SuperTapir/CadenzaOS/assets/typography/review/2026-07-19/typography-matrix-index.md

# Typography visual matrix

Columns: T-Embed 320×170, Sharp 400×240.

1. `launcher`
2. `timer-ready`
3. `timer-running`
4. `timer-paused`
5. `timer-alert`
6. `timer-starting-mid`
7. `timer-pausing-mid`
8. `timer-resuming-mid`
9. `timer-alert-mid`
10. `motion`
11. `settings`
12. `gallery-easing`
13. `gallery-selection`
14. `gallery-sprite`
15. `system-menu`
16. `system-overlay`
17. `role-long-inverse`

Contact sheet: `typography-contact-sheet.png`
