SuperTapir/CadenzaOS/assets/launcher-covers/review/2026-07-19-non-timer-refresh/gallery/review.md

# ANIMATION GALLERY v1 visual review

- Exact title: pass (`ANIMATION GALLERY`, complete and immediately legible in both profiles).
- Bold layout: pass; the title forms full-width top and bottom stage walls rather than a left-title/right-object template.
- Functional hook: pass; one repeated figure appears in exactly three successive poses along one easing arc.
- Element budget: pass; no frame numbers, axes, secondary curves, particles, camera marks or unrelated icons.
- Hard-threshold recognition: pass at 350×155 and 280×124; title, three poses and single trajectory remain recognizable without gray.
- Tonal discipline: pass; one concentrated halftone field supports the stage depth without entering title counters.
- Contour cleanup: pass with five bands plus `--edge-cleanup`; nearest-neighbor 4× inspection shows regular title and figure contours without patterned halos.
- Visual approval: explicitly approved by the user in this task on 2026-07-19 (`ok`).
- Formal source SHA-256: `856bd02c42c6160959b00fe79b05e403dc9a1034ae98b91581be47714985e979`.
