SuperTapir/CadenzaOS/docs/app-handoff-reference-research.md

# App Handoff 与 System Menu 动效参考调研

日期：2026-07-19
适用 change：`align-app-cover-handoff`

## 结论

- Launcher 只拥有从轨道/card chrome 到 App 身份的系统交接；App 入场后半段不是统一模板，而是每款 App 独立的 launch sequence。
- 静态 Cover 与 launch sequence 必须分开：Cover 继续是不可变的目录身份，launch renderer 是可 seek、无 lifecycle side effect 的全屏纯绘制能力。
- 返回 Launcher 不倒放各 App 的入场动画，而使用当前 App 的静态 Cover bridge，形成更快的“收回卡片”语义。
- System Menu 是独立 system surface：右侧面板快速滑入、完整滑出；关闭期间底层 App 继续冻结且输入仍属于 Menu。

## 四段视频逐帧证据

| 文件 | 尺寸 / 时长 | 关键时间点 | 结论 |
|---|---:|---|---|
| `PixPin_2026-07-19_00-34-52.mp4` | 460×452 / 5.75 s | 约 2.85 s 启动；3.00 s chrome 退场；3.15–3.20 s dither 到黑；3.65 s App 首屏 | 系统先完成 Card/Launcher 交接，再揭示 App |
| `PixPin_2026-07-19_00-46-18.mp4` | 660×654 / 5.625 s | 约 1.25 s pressed 反馈；1.75–1.95 s chrome 退场；2.05–3.65 s `MUSIC BOX` 专属标题/扫描线；3.75 s 曲目 UI | launch sequence 属于 Music Box 自身，不是统一系统缩放 |
| `PixPin_2026-07-19_00-47-57.mp4` | 622×376 / 5.792 s | 约 1.85 s Launcher chrome 消失；人物画面继续占满屏幕并持续变化 | 另一 App 使用完全不同的内容连续入场 |
| `PixPin_2026-07-19_00-50-54.mp4` | 946×506 / 4.5 s / 24 FPS | 1.208 s 尚未出现，1.250–1.417 s 为 5 个打开关键帧；3.833 s 稳定，3.875–4.042 s 为关闭形变，4.083 s 已离屏 | 打开顶部首帧到位、底部以近似 `out-cubic` 追上；关闭仍由顶部先离开而非倒放；底层 App 全程冻结可见 |

最初抽帧使用本机 FFmpeg 7.1，以 10 FPS contact sheet 和转场区间 20 FPS 复核。2026-07-19 的菜单二次校准改用 AVFoundation 按源视频 24 FPS 逐帧提取：打开前缘从左上到右下，第一可见帧顶部已在最终分界而底部仍接近屏幕右缘；随后底部可见比例约按 `0 → 0.5 → 0.87 → 1` 收束。关闭前缘方向反转为右上到左下，证明它不是打开帧的简单倒序。这些时间点用于确定阶段、曲线和数量级，不作为未经真机批准的永久像素 golden。

## 锁定上游契约

本机 Playdate SDK 固定为 1.12.3。`Inside Playdate.html` 明确规定：

- `card.png` 为 350×155；
- Launcher 在启动动画前把 card 放在 400×240 的 `(25, 43, 350, 155)`；
- `launchImages/1.png, 2.png, ...` 是每个 game 自己提供的 400×240 全屏 transition frames；
- `launchImage.png` 是 loading/末帧 fallback。

`Examples/Level 1-1/Source/SystemAssets` 的 `card.png`/`card-pressed.png` 均为 350×155，`launchImages/1..9.png` 均为 400×240；关键源码和资产尺寸已直接检查，没有只依赖 README。Cadenza 只采用“静态 Card -> 每 App 全屏序列 -> 首屏”的职责划分，不复制 SDK 示例像素、声音或品牌。

## 既有开源证据复用

本 change 复用 `docs/reference-research.md` 已锁定的源码级调研：

- NobleEngine `93ffd6eb29d61c1af1cb8d40b78daf75c4e85946`：采用 Cover transition 的中点 lifecycle 交接思想；不采用 Lua scene engine、logo 或 transition assets。
- Taxman Engine `51981885dcb9bb7b467cb578785ac68a084fd8ab`：采用 off-screen/dither 对场景合成有价值的结论；不采用 `calloc/realloc` render textures 与完整 ECS。
- LVGL `a73e59f6d144785012e44ab93f1f3d4dde48a180` / Tweeny `d50d96dfa61b115fb0d9fce59f7bbe4488f9b9b0`：采用可 seek/确定性时间语义；不采用动态 descriptor/callback 容器。

## 采用 / 不采用

采用：App 独立 const launch renderer、归一化 progress、系统中点 lifecycle、两张固定 framebuffer、ordered dither、Menu 显式 closing 状态、双 profile 快照与真机 P8。

不采用：给静态 Cover 增加 launching 状态、运行时缩放已二值化 Cover、第三张全屏 transition buffer、提前 `onEnter`、外部 PNG/PDI 文件协议、倒放 App launch sequence 作为返回、Menu close 瞬切。

## 2026-07-19 实现与验证记录

实现采用两阶段 handoff：默认 Launcher → App 为 0.80 秒，App → Launcher 为 0.44 秒；Reduced Motion 分别为 0.56 秒和 0.28 秒。Timer、Motion、Settings、Animation Gallery 均提供独立的代码原生全屏 launch renderer；未实现该能力的 App 使用居中的静态 Cover/受约束名称卡。System Menu 在右边缘锚定，逐 scanline 形成斜向前缘，并把完整面板横向重采样进当前可见宽度；Resume 关闭期间仍冻结 App、消费输入，Home 则直接交给 return handoff，避免叠加两条系统动画。

首轮视觉审阅指出 Cover、独立概念动画与真实 App UI 仍是三段不连续构图。连续版因此取消中间海报：progress 0 逐像素等于居中 Cover，progress 1 逐像素等于同一 App 状态和 SystemSnapshot 在 `onEnter` 后的真实首屏，中间以固定相位 ordered-dither 单调交接像素。Settings launch renderer 接收只读 AppRenderContext，避免 Motion/Sound/Connectivity 非默认状态在中点跳变；Timer、Motion、Settings 抽取与普通 render 共用的首屏 helper，Gallery 使用与 page 0/Easing 完全一致的初始帧 helper。

菜单二次校准把 Normal 开关时长从 0.16 秒调整为 0.20 秒。打开不再让整个面板统一 `out-quad` 平移，也不再使用只有 28% 的浅逐行 stagger；顶部 scanline 在第一可见帧直接锚定最终左边界，底部先等待 22% 行程再按 `out-cubic` 追上，各行线性插值形成强斜边并继续横向重采样内容。关闭单独建模：顶部立即向右离开，底部延迟 40% 行程后跟随。真实 HeadlessHost 以 24 FPS 捕获后，打开底部轨迹约为 `0 → 0.58 → 0.89 → 0.99 → 1`，与参考逐帧估计的 `0 → 0.5 → 0.87 → 0.99 → 1` 接近；关闭斜边方向、约 5 帧形变和 0.20 秒端点同样一致。这样保留端点与两 framebuffer/零分配约束，同时复现参考中的拉伸与回收方向；Reduced Motion 仍为 0.10 秒。

返回动画的完整 30 FPS 审阅又发现：原 `inOutQuad` 把 App → Cover 的 dither 变化集中到中间两帧，T-Embed 的旧 Clock/Gallery 峰值为 20.96%/21.50%，Sharp 最坏达到 22.90%；同时 Sharp 的 bridge 使用整数向下居中落在 `y=42`，与 Launcher 和 Playdate card 契约的 `(25,43,350,155)` 相差 1 px。修订后前半段改为匀速 threshold 交接，奇数剩余空间统一用向上取整的视觉中心；中点后 Cover 内容矩形逐像素保持不动，只让边框、scanline 与相邻卡片恢复。新版 T-Embed 四 App 峰值依次为 11.70%、7.07%、8.02%、12.23%，Sharp 为 12.17%、7.92%、8.49%、13.05%，均低于 16% 回归上限。

自动化验证结果：

- `cmake --build build -j4`：通过；
- `ctest --test-dir build --output-on-failure`：71/71 通过；
- 独立 `-Wall -Wextra -Wpedantic -Werror` 构建与 handoff/allocation/apps/snapshot/desktop focused suite：通过；
- 双 profile golden：四个内置 App 入场、无专属 renderer fallback、旧 Clock 返回、Menu opening/closing 均已生成 PNG 目检并锁定 hash；四 App 另以固定 30 FPS 生成完整进入与返回 PNG/GIF 时间轴；该记录描述迁名前的历史资产。
- endpoint regression 证明四 App `p0 == Cover`、`p1 == first App frame`；30 FPS 相邻帧变化不超过 framebuffer 像素的 20%；
- return regression 证明四 App 在双 profile 下 `p0 == outgoing App frame`，生命周期中点后的 Cover 矩形与 Launcher 逐像素一致且固定，`p1` 后下一帧不跳变；30 FPS 相邻变化不超过 16%；
- 完整进入 → Menu 开合 → 返回路径的 `operator new/new[]` 计数保持不变；host `AppRuntime` 为 24,928 B，其中两张固定 framebuffer 为 24,048 B，没有第三张全屏 buffer；
- PlatformIO T-Embed compile：RAM 99,248 / 327,680 B（30.3%），Flash 412,449 / 3,145,728 B（13.1%）。相对 WIP 前的 `HEAD` 基线增加 64 B RAM、3,452 B Flash；连续进入/返回版相对首轮海报式 WIP 减少 1,048 B Flash；
- Sharp launch renderer 的一次性 host 微基准平均约 1.74 ms/帧；它只用于发现明显退化，不替代 ESP32 真机 frame-time；
- 两 profile SDL dummy 各运行 180 帧、desktop input smoke、共享源码审计、OpenSpec strict 与 `git diff --check` 均通过。

自动化只批准像素确定性和系统语义。T-Embed 真机仍需以 30 FPS 检查 Memory LCD 的 dither 闪烁、拖影、0.80 秒入场是否拖沓、0.44 秒返回是否干脆，以及菜单 0.16 秒形变是否与参考视频一致；这些是 P8 人工视觉批准边界，host PNG 不能代替。
