SuperTapir/CadenzaOS/assets/launcher-covers/review/2026-07-19-about/about/prompt.md

# Cadenza OS About Logo v1 prompt record

## Identity brief

Cadenza OS 是承载个人小游戏、工具、动画与互动实验的创作平台；一枚开放的巨型 C 环同时暗示旋钮、唱片槽与留给创作者自由发挥的华彩空间，精确字标 `CADENZA OS` 从开口穿出，在黑白主质量与两块结构灰面中形成冷静、鲜明的系统身份。

## Visual strategy

`retro software package`，不使用 App Cover 的截图或设置面板语言。

## Permitted elements

1. 精确字标 `CADENZA OS`；
2. 一个开放式粗 C 环；
3. 一条与字标锁合的宽基线；
4. 最多一个节拍 / 旋钮定位缺口。

## Tonal plan

- 主黑质量：C 环外轮廓、字标主面与基线；
- 主白质量：安静背景、开放 C 内部和字母 counter；
- 中灰面：C 环侧壁，表达厚度；
- 浅灰面：字标或基线的单一侧面，表达遮挡顺序。

## Generation prompt

Use case: logo-brand
Asset type: Cadenza OS About-screen identity lockup, prepared as a 350:155 micro-poster master
Primary request: Design an original Cadenza OS identity lockup whose recall hook is one enormous open C-shaped ring. The ring simultaneously suggests a rotary control, a record groove, and an open space for personal improvisation. The exact wordmark `CADENZA OS` emerges through the opening and locks into one broad baseline. The wordmark stays flat, frontal, complete, and instantly readable; the ring may sit behind and partly around it with an unambiguous occlusion order. Use only the exact wordmark, the open C ring, the broad baseline, and at most one bold index notch. Do not invent an icon family or extra symbols.
Input images: the four existing CadenzaOS Launcher Cover masters are style references only; do not copy their individual layouts or objects.
Scene/backdrop: one broad quiet field, balanced black and white masses, no external frame.
Style/medium: original restrained industrial monochrome software-package mark, bold editorial geometry, smooth high-resolution illustration designed for later ordered-dither conversion.
Composition/framing: strict landscape 350:155 ratio, safe crop for 1400x620, wordmark carries roughly half the visual weight, complete title inside generous safe margins.
Color palette: pure black, white, one middle gray side wall, one light gray overlap plane only.
Text (verbatim): `CADENZA OS` — spell C-A-D-E-N-Z-A, space, O-S, exactly once; no other text.
Constraints: hard pure-black-and-white threshold must preserve the wordmark, open C silhouette, and their overlap; critical contours broad and continuous; three to five discrete hard-boundary planes; smooth antialiased master edges; distinctive but compatible with the existing CadenzaOS TIMER, MOTION, SETTINGS, and ANIMATION GALLERY micro-posters.
Avoid: imitation of a specific Playdate cover or logo, copied lettering, musical notes, treble clefs, waveforms, keyboards, gears, circuit boards, settings controls, dashboards, buttons, screws, bolts, tiny labels, decorative ticks, multiple rings, external card frame, rounded container, generic mobile UI, photorealism, studio lighting, continuous gradients, soft shadows, contact shadows, ambient occlusion, glossy bevels, specular highlights, blur, random texture, pre-pixelated jagged edges, extra words, misspelling.

Shared medium direction: original restrained industrial 1-bit micro-poster identity art for a reflective monochrome handheld, exact title integrated as a large immediately legible primary graphic occupying roughly one third to one half of the composition, one instantly memorable relationship, bold black and white massing that preserves both title and hook under a hard pure-black-and-white threshold before any texture, large legible silhouettes, purposeful editorial composition, radical visual economy, coherent cool industrial house style, high-resolution smooth master designed for later 1-bit ordered-dither conversion, deliberate gray values used only as broad planar surfaces that clarify front face, side face and overlap, dimensional through scale and overlap rather than decorative clutter, no card border, landscape 350:155 aspect ratio, title fully inside safe margins.

## v1 review — rejected

The generated v1 is rejected before conversion. Although the title is exact and
the silhouette is strong, the oversized C reads as a generic mechanical dial or
hardware-company emblem. It does not communicate Cadenza's defining idea: a
stable system that deliberately leaves room for personal improvisation. The
mark also has no space for the requested elegant slogan. It must not become a
formal asset.

## v2 identity brief

一个克制、稳定的 `CADENZA` 主字标代表统一系统结构，紧凑的 `OS` 铭牌扣在末端；唯一一条自由笔势从严格基线中逸出、穿过字标并舒展开来，表达“规则中的即兴”，花体 slogan `A Space to Improvise.` 沿这条笔势落下。

## v2 permitted elements

1. 精确主字标 `CADENZA`；
2. 精确小型铭牌 `OS`；
3. 一条从规整基线逸出的连续自由笔势；
4. 精确 slogan `A Space to Improvise.`。

## v2 tonal plan

- 主白质量：宽阔、安静的背景与字母 counter；
- 主黑质量：`CADENZA` 字标和严格基线；
- 中灰面：自由笔势经过字标背后的单一遮挡段；
- 浅灰面：`OS` 铭牌的单一侧面。

## v2 concept review — rejected before generation

The free-stroke wordmark remains too abstract. It would explain the idea only
after reading a design rationale, rather than making Cadenza vivid at a glance.

## v3 identity brief

`CADENZA` 字标直接构成一座开放舞台 / 幕框，一位唯一的 solo performer 从规整结构中走进一束宽聚光平面自由发挥；紧凑的 `OS` 铭牌属于舞台结构，花体 slogan `A Space to Improvise.` 像签名落在下方。舞台是“为个人作品提供空间”，solo moment 是音乐术语 cadenza 的直接形象。

## v3 permitted elements

1. 精确主字标 `CADENZA`，同时充当舞台结构；
2. 精确小型铭牌 `OS`；
3. 一位大轮廓、无具体身份的 solo performer；
4. 一束宽聚光平面；
5. 精确 slogan `A Space to Improvise.`。

## v3 tonal plan

- 主白质量：舞台外的安静背景与开放空间；
- 主黑质量：字标舞台和人物轮廓；
- 中灰面：宽聚光平面，用于把人物从结构中分离；
- 浅灰面：舞台单一侧面，用于表达开口与深度。

## v3 concept review — superseded before generation

A generic performer and spotlight are pictorial, but the scene still needs a
specific musical object to make the name Cadenza immediate rather than merely
theatrical.

## v4 identity brief

一架高度简化的三角钢琴以打开的琴盖形成唯一大剪影，同时像向个人创作展开的舞台；精确字标 `CADENZA OS` 成为琴身侧面的结构，花体 slogan `A Space to Improvise.` 像演奏者签名沿下方落下。它以一个物件直接表达 cadenza 的独奏、优雅与自由发挥。

## v4 permitted elements

1. 精确主字标 `CADENZA OS`；
2. 一架高度简化的三角钢琴，仅保留琴身、打开的琴盖与一段宽键盘；
3. 精确花体 slogan `A Space to Improvise.`。

## v4 tonal plan

- 主白质量：安静背景、字标与琴键间隙；
- 主黑质量：钢琴连续外轮廓与字标支撑面；
- 中灰面：打开的琴盖内面，表达舞台式展开；
- 浅灰面：琴身唯一侧面，表达字标所在结构。
