SuperTapir/CadenzaOS/assets/launcher-covers/review/2026-07-19-non-timer-refresh/settings/review.md

# SETTINGS v1 visual review

- Exact title: pass (`SETTINGS`, once, complete and immediately legible in both profiles).
- Bold layout: pass; the title spans the center as the deck faceplate and does not reuse a left-title/right-object template.
- Functional hook: pass; rotary dial, toggle and slider form one tactile deck on a common base.
- Element budget: pass; no list, labels, Wi-Fi icon, screws, calibration ticks, extra panel or floating prop.
- Hard-threshold recognition: pass at 350×155 and 280×124; title and three control categories survive without gray.
- Hierarchy: pass; the bottom slider is intentionally subordinate but remains at least two pixels thick and readable as a horizontal control at 1×.
- Tonal discipline: pass; gray is limited to broad top/front/side deck planes.
- Contour cleanup: pass with five bands plus `--edge-cleanup`; nearest-neighbor 4× inspection shows clean title/control silhouettes without Bayer fringe touching critical edges.
- House distinction: pass; the central full-width deck differs from TIMER's overlap and MOTION's left-low kinetic wordmark.
- Grayscale-master style: fail after formal reflective review; continuous studio lighting, soft contact shadows, ambient occlusion and rounded product-render bevels make the 1-bit result read like a converted photograph rather than an illustration.
- Outer silhouette: fail after formal reflective review; the pale top plane and dithered side plane do not create a sufficiently continuous, independent deck contour.
- Visual approval: withdrawn after the user reviewed the formal reflective output on 2026-07-19. Preserve this candidate as rejected v1; do not use it as a formal baseline.
