SuperTapir/CadenzaOS/openspec/changes/archive/2026-07-18-add-bounded-text-layout/proposal.md

## Why

Cadenza 当前允许菜单调用方以固定倍数绘制动态文本，却不要求声明可用区域或溢出行为。因此，较长的应用名称和菜单信息会被截断、越过容器边界，或侵占相邻元素；虽然 framebuffer 的内存仍然安全，但最终菜单呈现已经失效。

## What Changes

- 增加确定性的受约束文本布局契约：绘制前，先根据调用方提供的矩形区域测量文本。
- 显式支持自适应缩放、省略号截断、换行和跑马灯等溢出策略；文本在最小倍数下仍无法容纳时，必须执行稳定且明确的降级行为。
- 将“内容约束”与“呈现方式”分离：裁剪只作为最终安全边界，布局阶段必须在光栅化之前选出完整且符合预期的呈现结果。
- 将 Launcher 主标题、左右相邻应用名及其他动态菜单标签从固定倍数绘制迁移到受约束布局。
- 为菜单中的主内容、次要标签、导航指示器和边框划分互不侵占的显式区域。
- 为两种受支持的 framebuffer profile、超长异常文本以及菜单元素互不重叠补充回归测试。

## Capabilities

### New Capabilities

- `bounded-text-layout`：规定动态文本在受限 UI 区域内进行确定性测量、自适应、降级和边界约束的行为，并规定菜单消费者如何为动态标签分配独立区域。

### Modified Capabilities

无。仓库目前没有已归档的主 spec；Launcher 的采用行为统一记录在新 capability 中。

## Impact

- 影响可移植的 `MonoCanvas` 文本 API，或建立在其上的小型 presentation 层辅助模块；同时影响 Launcher 的动态文本绘制与菜单区域划分。
- 不改变 framebuffer 尺寸、应用切换逻辑、输入语义或桌面调试 HUD 的现有覆盖式呈现。
- 增加可移植布局测试，以及 Launcher 在 320×170 和 400×240 下的快照、边界和元素重叠回归用例。
- 不引入新的运行时依赖，固件侧不新增预期 heap 分配；布局结果必须保持确定性，并适配固定容量约束。
