SuperTapir/CadenzaOS/assets/industrial-design/3d/cadenza-concept-v1-back.png

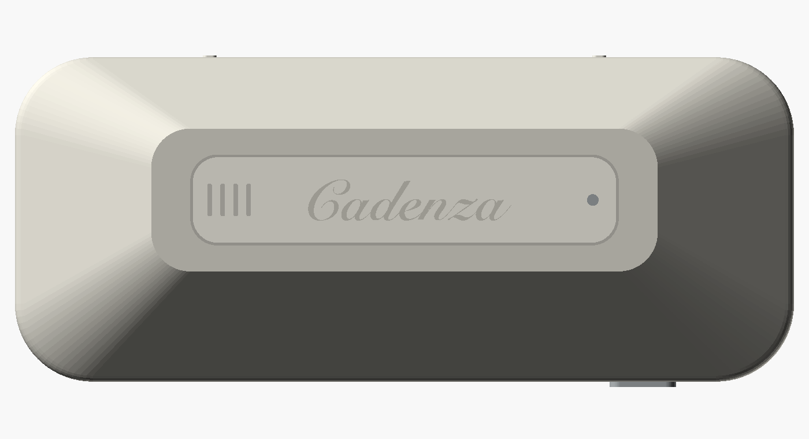
assets/industrial-design/3d/cadenza-concept-v1-back.png
