SuperTapir/CadenzaOS/assets/industrial-design/3d/cadenza-concept-v1-front.png

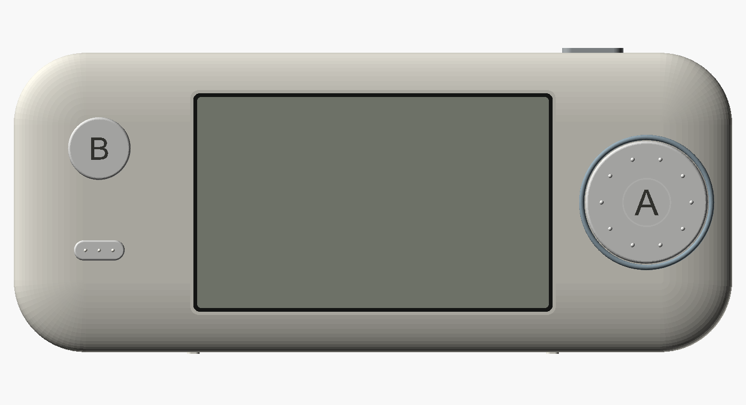
assets/industrial-design/3d/cadenza-concept-v1-front.png
