SuperTapir/CadenzaOS/assets/industrial-design/3d/cadenza-concept-v1-side.png

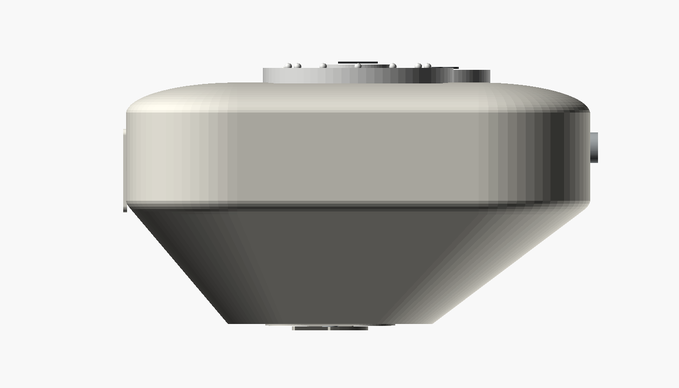
assets/industrial-design/3d/cadenza-concept-v1-side.png
