SuperTapir/CadenzaOS/assets/launcher-covers/review/2026-07-19-about/about/v6/full-screen/sharp-about.png

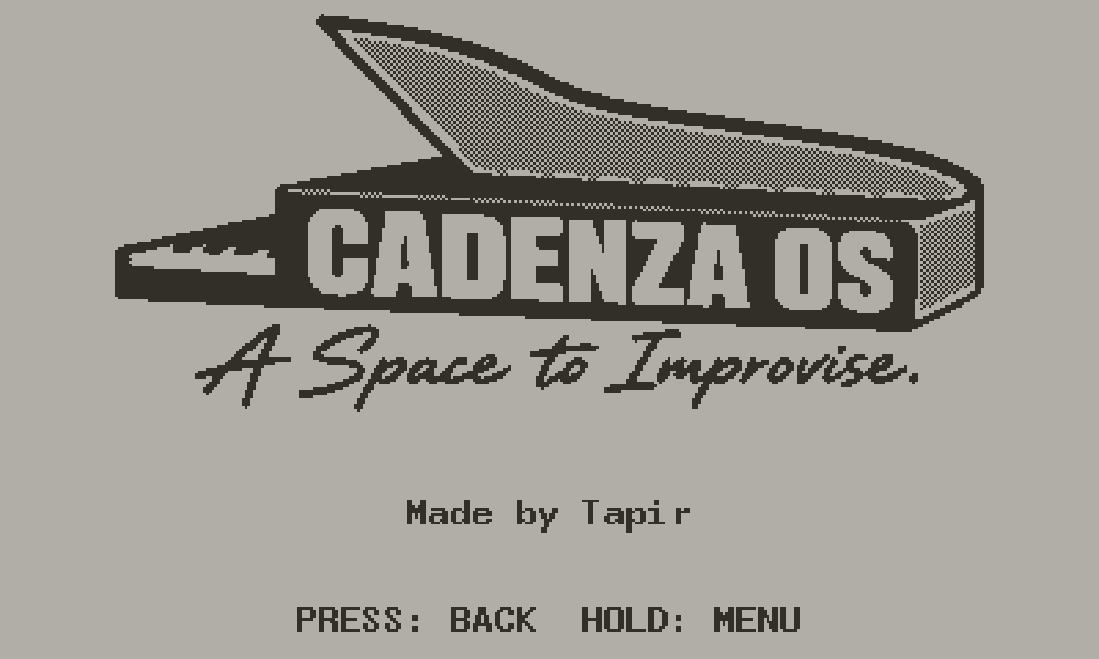
assets/launcher-covers/review/2026-07-19-about/about/v6/full-screen/sharp-about.png
