SuperTapir/CadenzaOS/assets/launcher-covers/review/2026-07-19-non-timer-refresh/gallery/candidate/gallery-v1-contours-4x.png

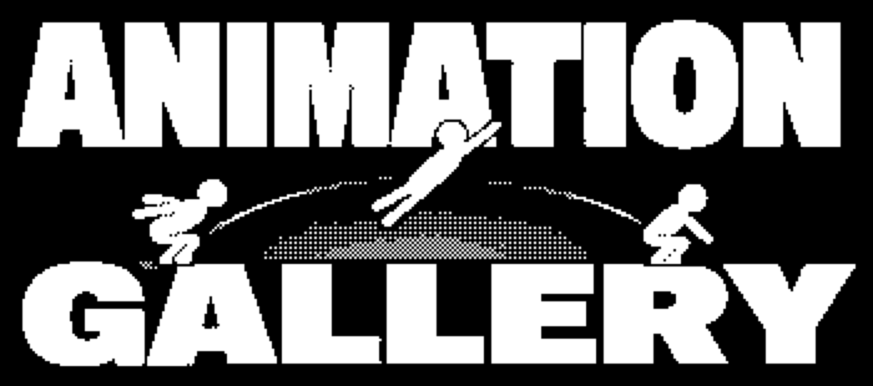
assets/launcher-covers/review/2026-07-19-non-timer-refresh/gallery/candidate/gallery-v1-contours-4x.png
