SuperTapir/CadenzaOS/assets/launcher-covers/review/2026-07-19-non-timer-refresh/gallery/candidate/review/gallery-v1_t_embed_1bit.png

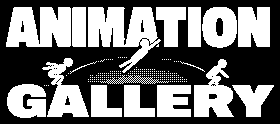
assets/launcher-covers/review/2026-07-19-non-timer-refresh/gallery/candidate/review/gallery-v1_t_embed_1bit.png
