SuperTapir/CadenzaOS/assets/launcher-covers/review/2026-07-19-non-timer-refresh/motion/edge-cleanup/motion-before-after-4x.png

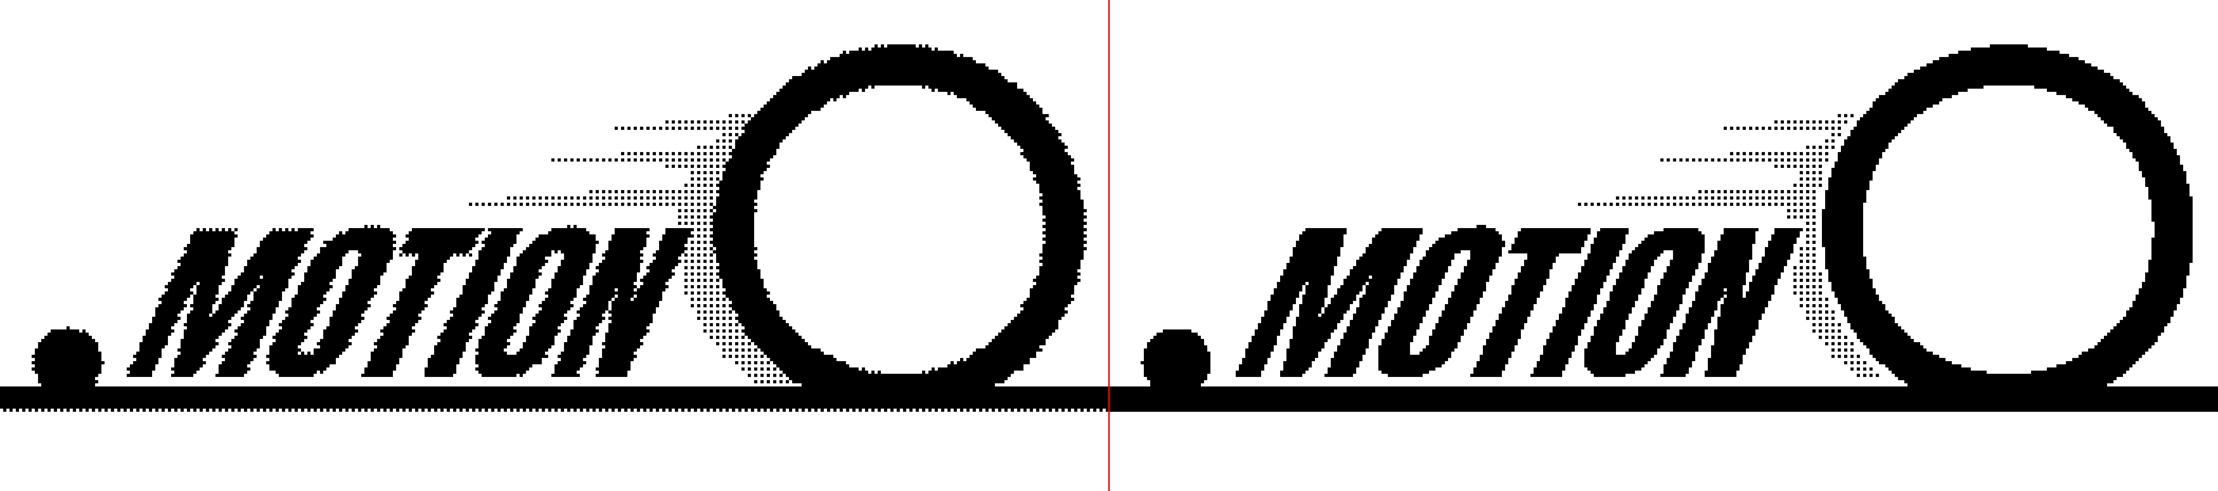
assets/launcher-covers/review/2026-07-19-non-timer-refresh/motion/edge-cleanup/motion-before-after-4x.png
