SuperTapir/CadenzaOS/assets/launcher-covers/review/2026-07-19-non-timer-refresh/motion/edge-cleanup/review/motion_1bit.png

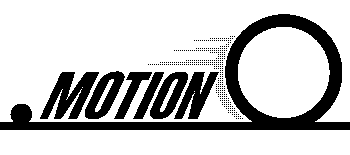
assets/launcher-covers/review/2026-07-19-non-timer-refresh/motion/edge-cleanup/review/motion_1bit.png
