SuperTapir/CadenzaOS/assets/launcher-covers/review/2026-07-19-non-timer-refresh/motion/source/motion-v1-original.png

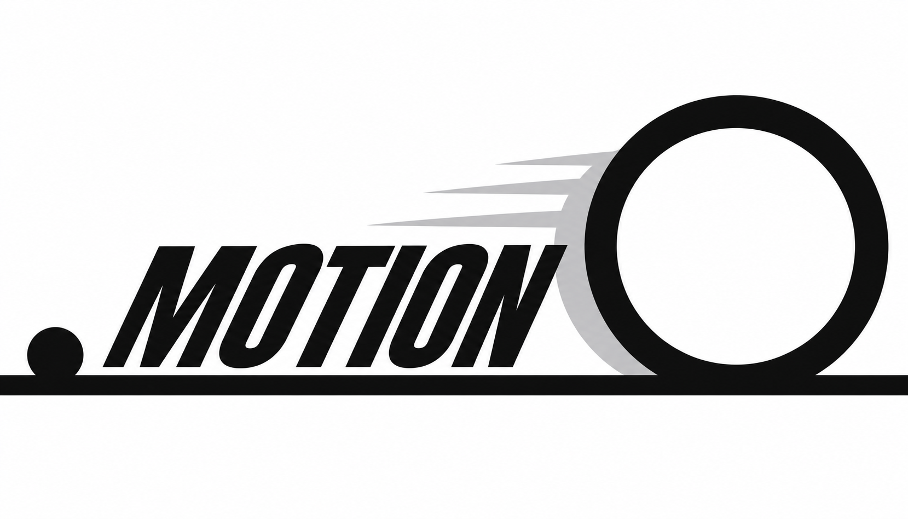
assets/launcher-covers/review/2026-07-19-non-timer-refresh/motion/source/motion-v1-original.png
