SuperTapir/CadenzaOS/assets/launcher-covers/review/2026-07-19-non-timer-refresh/settings/candidate/review/settings-v1_1bit.png

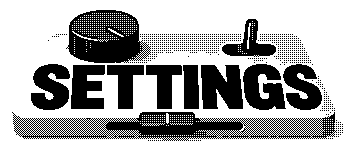
assets/launcher-covers/review/2026-07-19-non-timer-refresh/settings/candidate/review/settings-v1_1bit.png
