SuperTapir/CadenzaOS/assets/launcher-covers/review/2026-07-19-non-timer-refresh/settings/v2/candidate/review/settings-v2_1bit.png

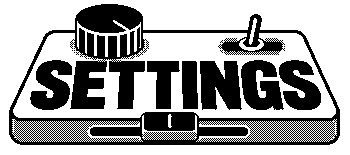
assets/launcher-covers/review/2026-07-19-non-timer-refresh/settings/v2/candidate/review/settings-v2_1bit.png
