SuperTapir/CadenzaOS/assets/launcher-covers/review/2026-07-19-timer-interlock-r-v2/review/timer-interlock-r-v2_1bit.png

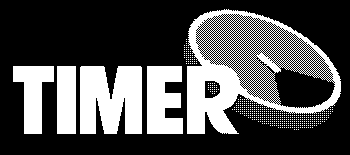
assets/launcher-covers/review/2026-07-19-timer-interlock-r-v2/review/timer-interlock-r-v2_1bit.png
