SuperTapir/CadenzaOS/assets/launcher-covers/review/2026-07-19-timer-time-mass/timer-gray-280x124.png

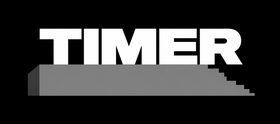
assets/launcher-covers/review/2026-07-19-timer-time-mass/timer-gray-280x124.png
