SuperTapir/CadenzaOS/assets/launcher-covers/review/2026-07-19-timer-title-hint/timer-title-hinted-280x124-title-4x.png

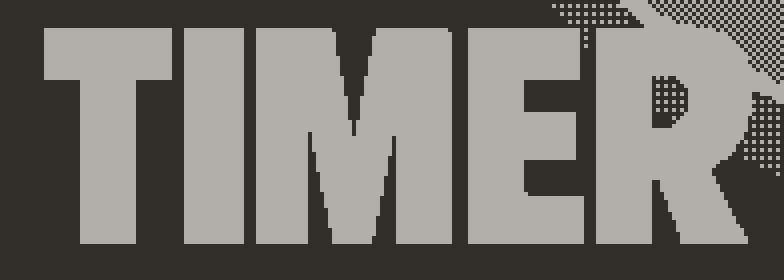
assets/launcher-covers/review/2026-07-19-timer-title-hint/timer-title-hinted-280x124-title-4x.png
