SuperTapir/CadenzaOS/assets/launcher-covers/review/2026-07-19/motion-v2-master-1400x620.png

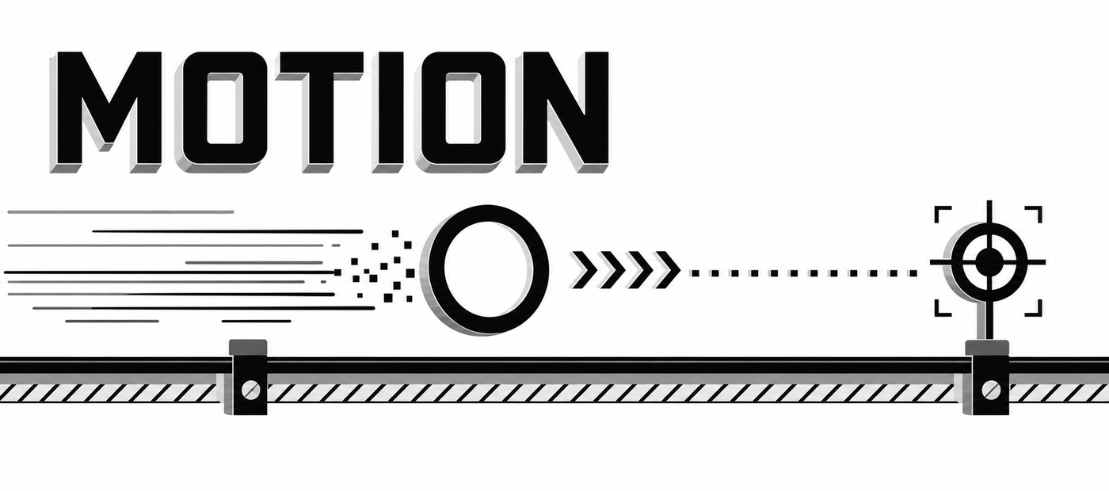
assets/launcher-covers/review/2026-07-19/motion-v2-master-1400x620.png
