SuperTapir/CadenzaOS/assets/launcher-covers/review/gallery_t_embed_threshold_4x.png

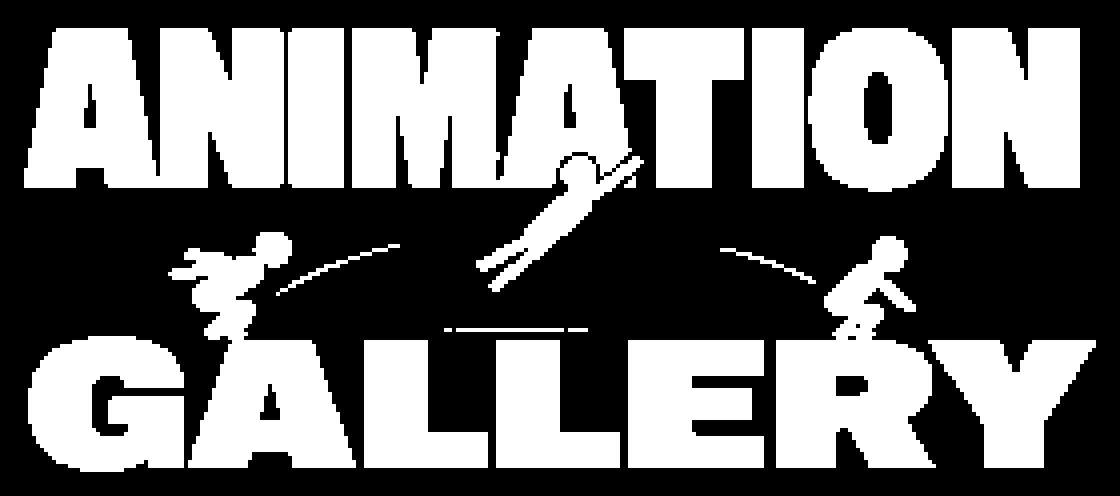
assets/launcher-covers/review/gallery_t_embed_threshold_4x.png
