SuperTapir/CadenzaOS/assets/launcher-covers/source/gallery.png

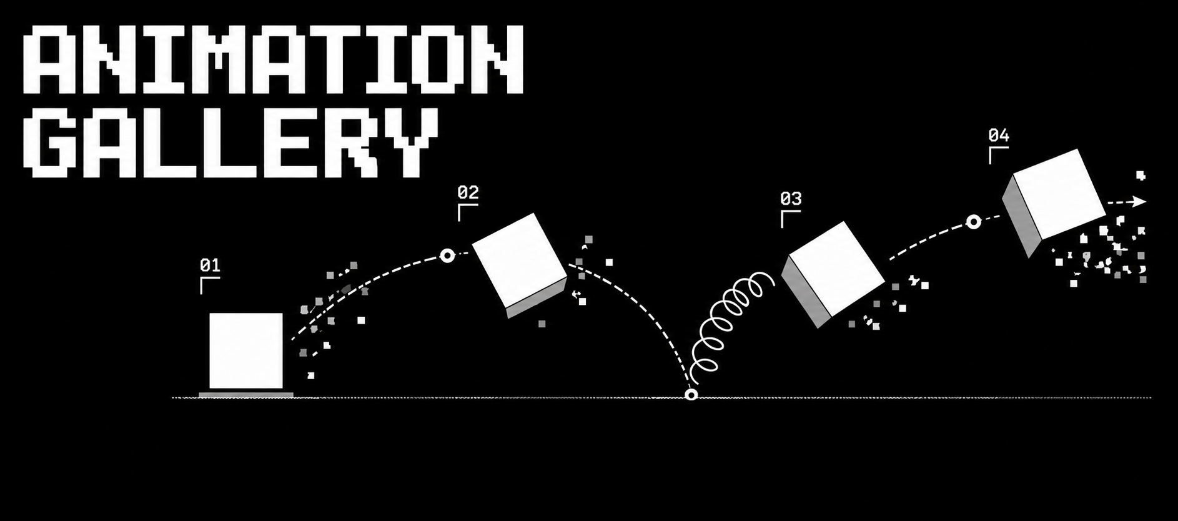
assets/launcher-covers/source/gallery.png
