SuperTapir/CadenzaOS/assets/launcher-covers/source/motion.png

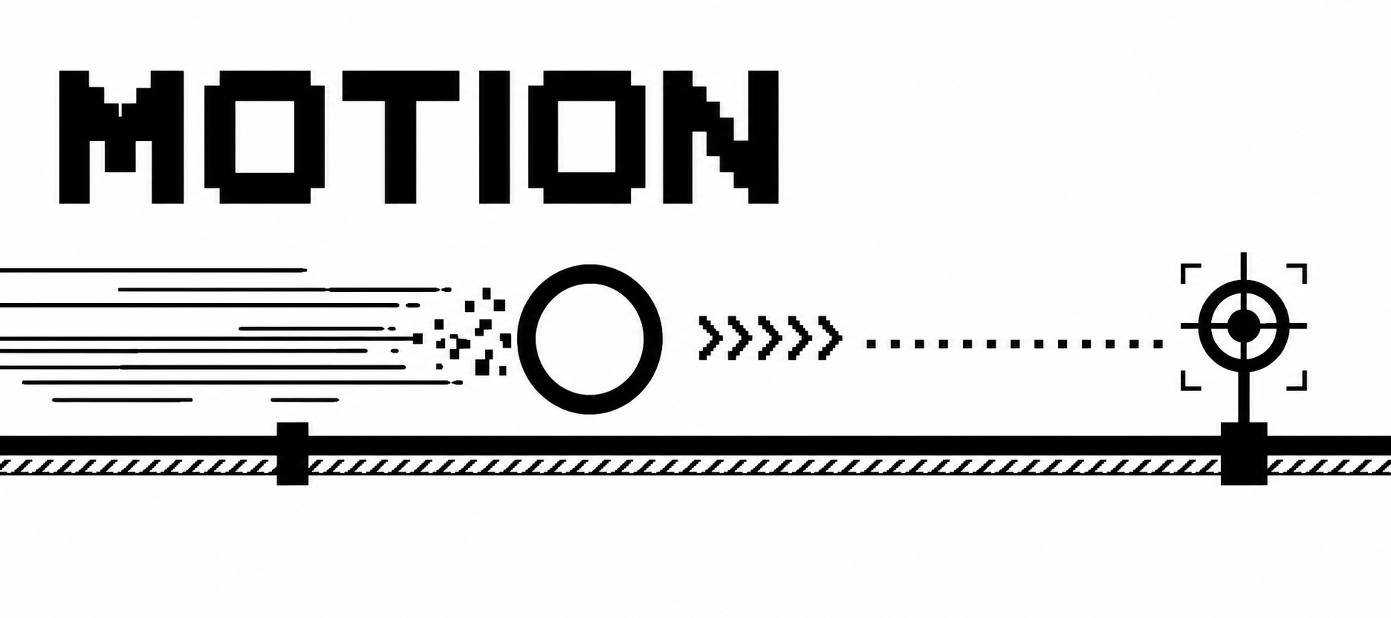
assets/launcher-covers/source/motion.png
