SuperTapir/CadenzaOS/assets/launcher-covers/source/settings.png

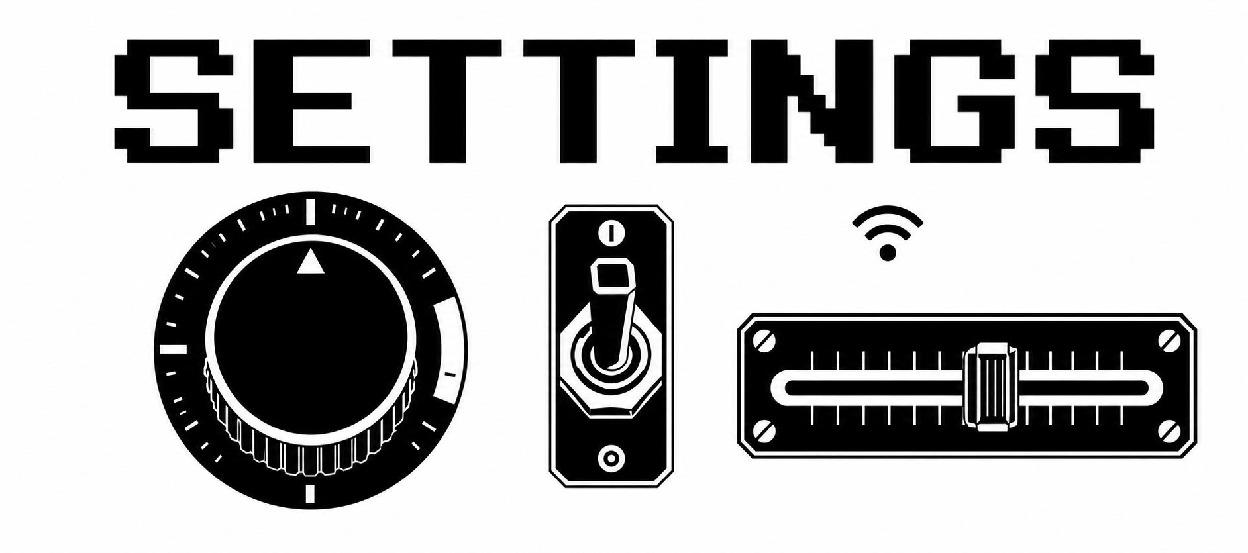
assets/launcher-covers/source/settings.png
