SuperTapir/CadenzaOS/assets/launcher-covers/source/sight.png

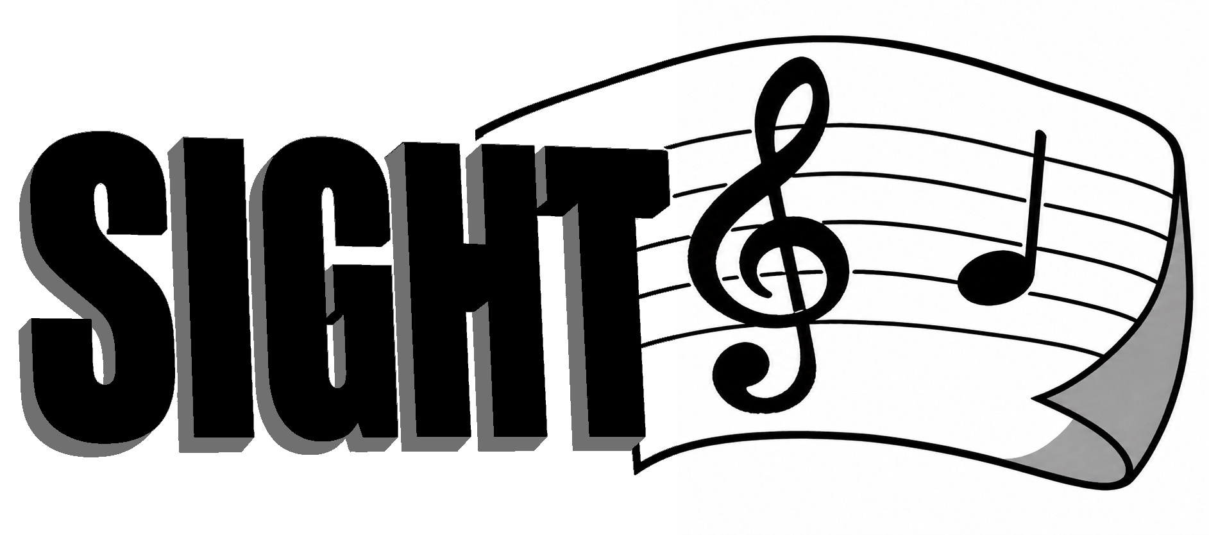
assets/launcher-covers/source/sight.png
