SuperTapir/CadenzaOS/assets/timer-alert/review/2026-07-19/240-alert-mid.png

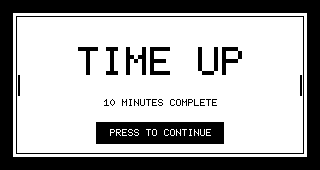
assets/timer-alert/review/2026-07-19/240-alert-mid.png
