SuperTapir/CadenzaOS/assets/timer-alert/review/2026-07-19/240-paused.png

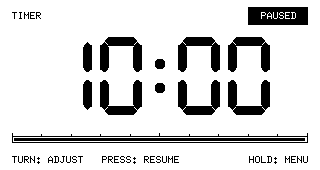
assets/timer-alert/review/2026-07-19/240-paused.png
