SuperTapir/CadenzaOS/assets/timer-alert/review/2026-07-19/240-settings-square-colon.png

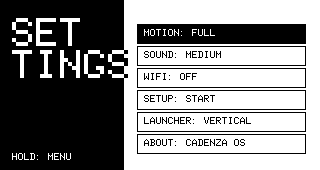
assets/timer-alert/review/2026-07-19/240-settings-square-colon.png
