SuperTapir/CadenzaOS/assets/timer-alert/review/2026-07-19/400-alert-mid.png

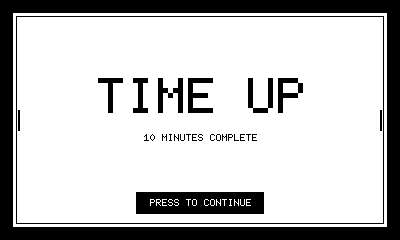
assets/timer-alert/review/2026-07-19/400-alert-mid.png
