SuperTapir/CadenzaOS/assets/timer-alert/review/2026-07-19/400-paused-playdate-colon.png

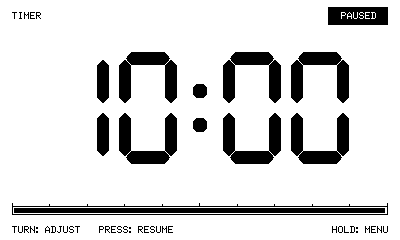
assets/timer-alert/review/2026-07-19/400-paused-playdate-colon.png
