SuperTapir/CadenzaOS/assets/timer-alert/review/2026-07-19/400-resuming-mid.png

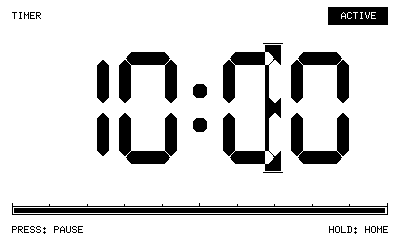
assets/timer-alert/review/2026-07-19/400-resuming-mid.png
