SuperTapir/CadenzaOS/assets/timer-digits/review/2026-07-19/timer-paused-320.png

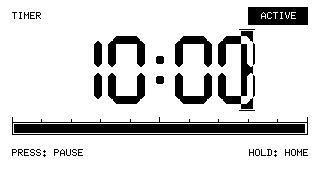
assets/timer-digits/review/2026-07-19/timer-paused-320.png
