SuperTapir/CadenzaOS/assets/typography/review/2026-07-19/typography-contact-sheet.png

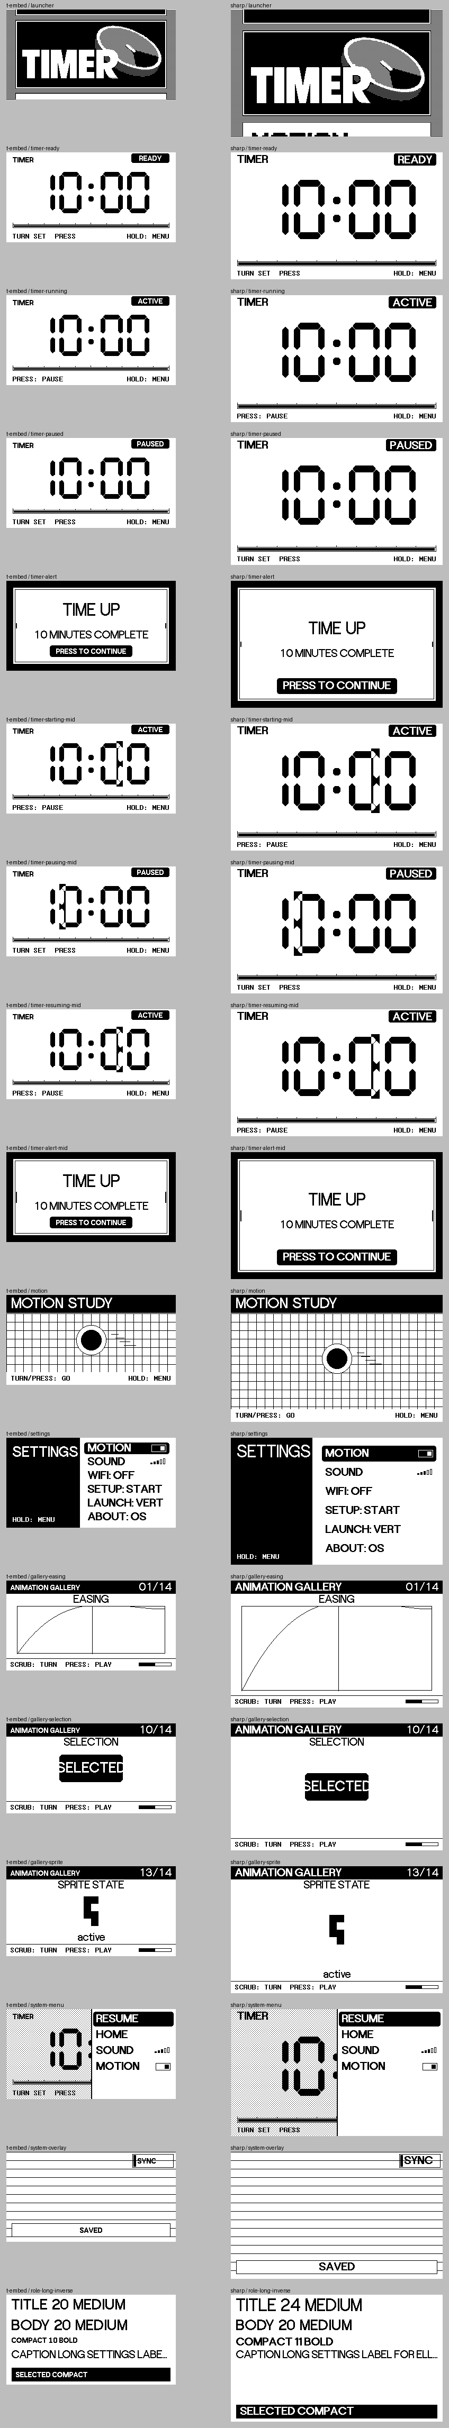
assets/typography/review/2026-07-19/typography-contact-sheet.png
