SuperTapir/CadenzaOS/assets/launcher-covers/review/2026-07-19/build-sight-reading-trainer/sight-illustrated-v3-dimensional/review.md

# SIGHT Launcher Cover 视觉批准记录

- App：`SIGHT`
- 批准日期：2026-07-19
- 批准对象：`candidate/review/sight_1bit.png` 与
  `candidate/review/sight_t_embed_1bit.png`
- 转换参数：`prepare_cover.py --levels 5 --edge-cleanup`
- 用户结论：卷开的五线谱构图可用；最终要求增强立体字灰阶，同时保持
  `SIGHT` 五个字母的白色分隔和清楚轮廓。

最终母版把标题限制为三个硬边色面：纯黑正面、统一灰色侧面和白色负空间；
五线谱纸保留纯黑轮廓与一处受控灰阶翻页。350×155 与 280×124 的纯黑白、
reflective、硬阈值和 4× nearest-neighbor 预览均已检查：标题拼写正确，无裁切，
谱线、谱号和音符可辨，字母没有再次合并，关键轮廓没有孤立毛刺。
