SuperTapir/CadenzaOS/tests/apps_tests.cpp

#define DOCTEST_CONFIG_IMPLEMENT_WITH_MAIN
#include "doctest.h"

#include <algorithm>
#include <array>
#include <cmath>
#include <cstring>
#include <vector>

#include "cadenza/apps/apps.h"
#include "cadenza/presentation/timer_numerals.h"
#include "app_context_test_support.h"

namespace {
bool hasBlackPixel(const cadenza::MonoFramebuffer& framebuffer) {
  return std::any_of(framebuffer.data(),
                     framebuffer.data() + framebuffer.sizeBytes(),
                     [](std::uint8_t byte) { return byte != 0; });
}

bool hasBlackInRect(const cadenza::MonoFramebuffer& framebuffer,
                    cadenza::Rect bounds) {
  for (int y = std::max(0, bounds.y);
       y < std::min<int>(framebuffer.height(), bounds.y + bounds.height); ++y) {
    for (int x = std::max(0, bounds.x);
         x < std::min<int>(framebuffer.width(), bounds.x + bounds.width); ++x) {
      if (framebuffer.pixel(x, y)) return true;
    }
  }
  return false;
}

class NamedApp final : public cadenza::App {
 public:
  explicit NamedApp(const char* value) : value_(value) {}
  const char* name() const noexcept override { return value_; }
  void update(const cadenza::AppUpdateContext&) noexcept override {}
  void render(cadenza::MonoCanvas&,
              const cadenza::AppRenderContext&) noexcept override {}

 private:
  const char* value_;
};

class CoverProbeApp final : public cadenza::App {
 public:
  explicit CoverProbeApp(const char* value) : value_(value) {}
  const char* name() const noexcept override { return value_; }
  void update(const cadenza::AppUpdateContext&) noexcept override {}
  void render(cadenza::MonoCanvas&,
              const cadenza::AppRenderContext&) noexcept override {}
  bool renderLauncherCover(cadenza::MonoCanvas& canvas,
                           cadenza::Rect bounds) const noexcept override {
    ++renderCount;
    minimumWidth = std::min(minimumWidth, bounds.width);
    maximumWidth = std::max(maximumWidth, bounds.width);
    canvas.rect(bounds.x, bounds.y, bounds.width, bounds.height, true);
    return true;
  }

  mutable int renderCount = 0;
  mutable int minimumWidth = 32767;
  mutable int maximumWidth = 0;

  void resetCoverObservations() const noexcept {
    renderCount = 0;
    minimumWidth = 32767;
    maximumWidth = 0;
  }

 private:
  const char* value_;
};

class TextDiagnosticSink final : public cadenza::DiagnosticSink {
 public:
  void emit(const cadenza::DiagnosticEvent& event) noexcept override {
    if (event.message && std::strcmp(event.message, "text clipped") == 0) {
      textClipped = true;
    }
    if (event.code == cadenza::DiagnosticCode::ClippedGeometry ||
        event.code == cadenza::DiagnosticCode::FullyClipped) {
      unexpectedGeometryClip = true;
    }
    if (event.code == cadenza::DiagnosticCode::InvalidGeometry) {
      invalidGeometry = true;
    }
  }
  bool textClipped = false;
  bool unexpectedGeometryClip = false;
  bool invalidGeometry = false;
};

std::uint64_t framebufferHash(const cadenza::MonoFramebuffer& framebuffer) {
  std::uint64_t hash = 1469598103934665603ULL;
  for (std::size_t index = 0; index < framebuffer.sizeBytes(); ++index) {
    hash ^= framebuffer.data()[index];
    hash *= 1099511628211ULL;
  }
  return hash;
}

std::size_t changedPixels(const cadenza::MonoFramebuffer& first,
                          const cadenza::MonoFramebuffer& second) {
  std::size_t changed = 0;
  for (std::size_t index = 0; index < first.sizeBytes(); ++index) {
    std::uint8_t bits = static_cast<std::uint8_t>(
        first.data()[index] ^ second.data()[index]);
    while (bits != 0) {
      changed += bits & 1U;
      bits >>= 1U;
    }
  }
  return changed;
}

cadenza::Rect changedBoundsIn(const cadenza::MonoFramebuffer& first,
                              const cadenza::MonoFramebuffer& second,
                              cadenza::Rect region) {
  int left = region.x + region.width;
  int top = region.y + region.height;
  int right = region.x - 1;
  int bottom = region.y - 1;
  for (int y = region.y; y < region.y + region.height; ++y) {
    for (int x = region.x; x < region.x + region.width; ++x) {
      if (first.pixel(x, y) == second.pixel(x, y)) continue;
      left = std::min(left, x);
      top = std::min(top, y);
      right = std::max(right, x);
      bottom = std::max(bottom, y);
    }
  }
  return right < left ? cadenza::Rect{}
                      : cadenza::Rect{left, top, right - left + 1,
                                      bottom - top + 1};
}

template <typename AppType>
bool registerBuiltin(cadenza::AppRuntime& runtime, cadenza::AppId id,
                     AppType& app, bool visible = true) {
  return runtime.registerApp(id, app, visible,
                             cadenza::apps::builtinAppCapabilities(id));
}

void registerNamedApps(cadenza::AppRuntime& runtime,
                       cadenza::LauncherApp& launcher, NamedApp& timer,
                       NamedApp& motion, NamedApp& settings,
                       NamedApp& gallery) {
  REQUIRE(registerBuiltin(runtime, cadenza::apps::kLauncherAppId, launcher, false));
  REQUIRE(registerBuiltin(runtime, cadenza::apps::kTimerAppId, timer));
  REQUIRE(registerBuiltin(runtime, cadenza::apps::kMotionAppId, motion));
  REQUIRE(registerBuiltin(runtime, cadenza::apps::kSettingsAppId, settings));
  REQUIRE(registerBuiltin(runtime, cadenza::apps::kGalleryAppId, gallery));
  REQUIRE(runtime.begin(cadenza::apps::kLauncherAppId));
}
}  // namespace

TEST_CASE("bundled Apps declare minimal capabilities and default deny") {
  using cadenza::AppCapability;
  for (const cadenza::AppId id : {
           cadenza::apps::kLauncherAppId, cadenza::apps::kTimerAppId,
           cadenza::apps::kMotionAppId, cadenza::apps::kGalleryAppId}) {
    const auto capabilities = cadenza::apps::builtinAppCapabilities(id);
    CHECK_FALSE(capabilities.contains(AppCapability::NetworkAcquire));
    CHECK_FALSE(capabilities.contains(AppCapability::ProvisioningManage));
    CHECK_FALSE(capabilities.contains(AppCapability::VoiceAnalyzer));
  }
  const auto settings = cadenza::apps::builtinAppCapabilities(
      cadenza::apps::kSettingsAppId);
  CHECK(settings.contains(AppCapability::NetworkAcquire));
  CHECK(settings.contains(AppCapability::ProvisioningManage));
  CHECK_FALSE(settings.contains(AppCapability::VoiceAnalyzer));
  CHECK(cadenza::apps::builtinAppCapabilities(cadenza::AppId{0x7FFF}) ==
        cadenza::AppCapabilitySet{});
}

TEST_CASE("all bundled Apps render through the portable canvas at both profiles") {
  for (const cadenza::FramebufferProfile profile : {
           cadenza::FramebufferProfile::TEmbed,
           cadenza::FramebufferProfile::Sharp}) {
    cadenza::LauncherApp launcher;
    cadenza::TimerApp timer;
    cadenza::MotionApp motion;
    cadenza::SettingsApp settings;
    cadenza::AnimationGalleryApp gallery;
    cadenza::AppRuntime runtime{profile, cadenza::kCutTransition};
    cadenza::system::SystemServiceHost services;
    REQUIRE(registerBuiltin(runtime, cadenza::apps::kLauncherAppId, launcher, false));
    REQUIRE(registerBuiltin(runtime, cadenza::apps::kTimerAppId, timer));
    REQUIRE(registerBuiltin(runtime, cadenza::apps::kMotionAppId, motion));
    REQUIRE(registerBuiltin(runtime, cadenza::apps::kSettingsAppId, settings));
    REQUIRE(registerBuiltin(runtime, cadenza::apps::kGalleryAppId, gallery));
    REQUIRE(runtime.begin(cadenza::apps::kLauncherAppId));

    cadenza::MonoFramebuffer framebuffer{profile};
    const std::array<cadenza::App*, 5> apps{
        &launcher, &timer, &motion, &settings, &gallery};
    for (std::size_t appIndex = 0; appIndex < apps.size(); ++appIndex) {
      CAPTURE(static_cast<int>(profile));
      CAPTURE(appIndex);
      cadenza::App* app = apps[appIndex];
      TextDiagnosticSink diagnostics;
      cadenza::MonoCanvas canvas{framebuffer, &diagnostics};
      framebuffer.clear(false);
      cadenza::test::renderApp(*app, canvas, runtime, services);
      CHECK(hasBlackPixel(framebuffer));
      CHECK_FALSE(diagnostics.textClipped);
    }
  }
}

TEST_CASE("Timer numeral atlases keep approved geometry and optical colon") {
  constexpr std::array<std::uint32_t, 3> values{
      10U * 60000U, 5U * 60000U, 1000U};
  for (const auto profile : {cadenza::FramebufferProfile::TEmbed,
                             cadenza::FramebufferProfile::Sharp}) {
    const int expectedWidth =
        profile == cadenza::FramebufferProfile::Sharp ? 308 : 228;
    const int expectedHeight =
        profile == cadenza::FramebufferProfile::Sharp ? 120 : 84;
    for (const std::uint32_t value : values) {
      CAPTURE(static_cast<int>(profile));
      CAPTURE(value);
      cadenza::MonoFramebuffer framebuffer{profile};
      TextDiagnosticSink diagnostics;
      cadenza::MonoCanvas canvas{framebuffer, &diagnostics};
      const auto metrics =
          cadenza::presentation::timerNumeralMetrics(canvas.width());
      const cadenza::Rect bounds =
          cadenza::presentation::renderTimerNumerals(canvas, value, 12);
      CHECK(bounds.x == (canvas.width() - expectedWidth) / 2);
      CHECK(bounds.y == 12);
      CHECK(bounds.width == expectedWidth);
      CHECK(bounds.height == expectedHeight);
      CHECK(metrics.displayWidth() == expectedWidth);
      CHECK(metrics.digitWidth * 4 + metrics.colonWidth == expectedWidth);
      CHECK_FALSE(diagnostics.unexpectedGeometryClip);
      CHECK_FALSE(diagnostics.invalidGeometry);

      const int colonLeft = bounds.x + metrics.digitWidth * 2;
      int inkLeft = colonLeft + metrics.colonWidth;
      int inkRight = colonLeft - 1;
      int rowBands = 0;
      bool previousRow = false;
      for (int y = bounds.y; y < bounds.y + bounds.height; ++y) {
        bool rowHasInk = false;
        for (int x = colonLeft; x < colonLeft + metrics.colonWidth; ++x) {
          if (!framebuffer.pixel(x, y)) continue;
          rowHasInk = true;
          inkLeft = std::min(inkLeft, x);
          inkRight = std::max(inkRight, x);
        }
        if (rowHasInk && !previousRow) ++rowBands;
        previousRow = rowHasInk;
      }
      REQUIRE(inkRight >= inkLeft);
      CHECK(rowBands == 2);
      const int inkCenterTwice = inkLeft + inkRight;
      const int cellCenterTwice = colonLeft * 2 + metrics.colonWidth - 1;
      CHECK(std::abs(inkCenterTwice - cellCenterTwice) <= 2);
    }
  }
}

TEST_CASE("portable Launcher opens the selected registered App") {
  cadenza::LauncherApp launcher;
  cadenza::TimerApp timer;
  cadenza::AppRuntime runtime;
    cadenza::system::SystemServiceHost services;
  REQUIRE(registerBuiltin(runtime, cadenza::apps::kLauncherAppId, launcher, false));
  REQUIRE(registerBuiltin(runtime, cadenza::apps::kTimerAppId, timer));
  REQUIRE(runtime.begin(cadenza::apps::kLauncherAppId));
  cadenza::InputFrame input;
  input.clicked = true;
  cadenza::test::updateRuntime(runtime, services, 1.0F / 60.0F, input);
  CHECK(runtime.transitioning());
  cadenza::test::updateRuntime(runtime, services, 0.41F);
  CHECK(runtime.currentId() == cadenza::apps::kTimerAppId);
}

TEST_CASE("App catalog forwards optional const Launcher Covers") {
  cadenza::LauncherApp launcher;
  NamedApp fallback{"Fallback"};
  CoverProbeApp covered{"Covered"};
  cadenza::AppRuntime runtime{cadenza::FramebufferProfile::TEmbed,
                              cadenza::kCutTransition};
  REQUIRE(registerBuiltin(runtime, cadenza::apps::kLauncherAppId, launcher,
                          false));
  REQUIRE(runtime.registerApp(cadenza::AppId{0x0201}, fallback, true));
  REQUIRE(runtime.registerApp(cadenza::AppId{0x0202}, covered, true));
  REQUIRE(runtime.begin(cadenza::apps::kLauncherAppId));

  cadenza::MonoFramebuffer framebuffer{cadenza::FramebufferProfile::TEmbed};
  cadenza::MonoCanvas canvas{framebuffer};
  const cadenza::AppCatalogView catalog = runtime.catalogView();
  cadenza::SystemSnapshot snapshot;
  const cadenza::AppRenderContext context{catalog, snapshot};
  CHECK_FALSE(catalog.renderLauncherCover(
      cadenza::AppId{0x0201}, canvas, {8, 8, 80, 48}));
  CHECK_FALSE(catalog.renderLaunchFrame(
      cadenza::AppId{0x0201}, canvas, 0.5F, context));
  CHECK(catalog.renderLauncherCover(
      cadenza::AppId{0x0202}, canvas, {8, 8, 80, 48}));
  CHECK(covered.renderCount == 1);
}

TEST_CASE("built-in launch sequences are deterministic seekable and distinct") {
  cadenza::TimerApp timer;
  cadenza::MotionApp motion;
  cadenza::SettingsApp settings;
  cadenza::AnimationGalleryApp gallery;
  const cadenza::App* apps[] = {&timer, &motion, &settings, &gallery};
  cadenza::AppCatalog emptyCatalog;
  const cadenza::AppCatalogView catalog{emptyCatalog};
  cadenza::SystemSnapshot snapshot;
  const cadenza::AppRenderContext context{catalog, snapshot};
  for (const auto profile : {cadenza::FramebufferProfile::TEmbed,
                             cadenza::FramebufferProfile::Sharp}) {
    std::array<std::uint64_t, 4> middleHashes{};
    for (std::size_t index = 0; index < 4; ++index) {
      cadenza::MonoFramebuffer first{profile};
      cadenza::MonoFramebuffer earlier{profile};
      cadenza::MonoFramebuffer repeated{profile};
      cadenza::MonoCanvas firstCanvas{first};
      cadenza::MonoCanvas earlierCanvas{earlier};
      cadenza::MonoCanvas repeatedCanvas{repeated};
      REQUIRE(apps[index]->renderLaunchFrame(firstCanvas, 0.65F, context));
      REQUIRE(apps[index]->renderLaunchFrame(earlierCanvas, 0.25F, context));
      REQUIRE(apps[index]->renderLaunchFrame(repeatedCanvas, 0.65F,
                                             context));
      middleHashes[index] = framebufferHash(first);
      CHECK(middleHashes[index] == framebufferHash(repeated));
      CHECK(middleHashes[index] != framebufferHash(earlier));
    }
    for (std::size_t left = 0; left < 4; ++left) {
      for (std::size_t right = left + 1; right < 4; ++right) {
        CHECK(middleHashes[left] != middleHashes[right]);
      }
    }
  }
}

TEST_CASE("built-in launch endpoints match Cover and first App frame") {
  for (const auto profile : {cadenza::FramebufferProfile::TEmbed,
                             cadenza::FramebufferProfile::Sharp}) {
    cadenza::LauncherApp launcher;
    cadenza::TimerApp timer;
    cadenza::MotionApp motion;
    cadenza::SettingsApp settings;
    cadenza::AnimationGalleryApp gallery;
    cadenza::App* apps[] = {&timer, &motion, &settings, &gallery};
    cadenza::AppRuntime runtime{profile, cadenza::kCutTransition};
    cadenza::system::SystemServiceHost services;
    REQUIRE(registerBuiltin(runtime, cadenza::apps::kLauncherAppId, launcher,
                            false));
    REQUIRE(registerBuiltin(runtime, cadenza::apps::kTimerAppId, timer));
    REQUIRE(registerBuiltin(runtime, cadenza::apps::kMotionAppId, motion));
    REQUIRE(registerBuiltin(runtime, cadenza::apps::kSettingsAppId, settings));
    REQUIRE(registerBuiltin(runtime, cadenza::apps::kGalleryAppId, gallery));
    REQUIRE(runtime.begin(cadenza::apps::kLauncherAppId));
    const cadenza::AppCatalogView catalog = runtime.catalogView();
    const cadenza::AppRenderContext context{catalog, services.snapshot()};
    for (cadenza::App* app : apps) {
      CAPTURE(app->name());
      cadenza::MonoFramebuffer cover{profile};
      cadenza::MonoFramebuffer launchStart{profile};
      cadenza::MonoFramebuffer launchEnd{profile};
      cadenza::MonoFramebuffer firstAppFrame{profile};
      cover.clear(true);
      const int width = std::min(350, cover.width() * 7 / 8);
      const int height = width * 155 / 350;
      cadenza::MonoCanvas coverCanvas{cover};
      cadenza::MonoCanvas startCanvas{launchStart};
      cadenza::MonoCanvas endCanvas{launchEnd};
      cadenza::MonoCanvas firstAppCanvas{firstAppFrame};
      REQUIRE(app->renderLauncherCover(
          coverCanvas, {(cover.width() - width) / 2,
                        (cover.height() - height + 1) / 2, width, height}));
      REQUIRE(app->renderLaunchFrame(startCanvas, 0.0F, context));
      REQUIRE(app->renderLaunchFrame(endCanvas, 1.0F, context));
      app->onEnter();
      app->render(firstAppCanvas, context);
      CHECK(framebufferHash(launchStart) == framebufferHash(cover));
      CHECK(framebufferHash(launchEnd) == framebufferHash(firstAppFrame));
    }
  }
}

TEST_CASE("built-in launch sequences have no 30 FPS full-frame jump") {
  for (const auto profile : {cadenza::FramebufferProfile::TEmbed,
                             cadenza::FramebufferProfile::Sharp}) {
    cadenza::TimerApp timer;
    cadenza::MotionApp motion;
    cadenza::SettingsApp settings;
    cadenza::AnimationGalleryApp gallery;
    const cadenza::App* apps[] = {&timer, &motion, &settings, &gallery};
    cadenza::AppCatalog emptyCatalog;
    const cadenza::AppCatalogView catalog{emptyCatalog};
    cadenza::SystemSnapshot snapshot;
    const cadenza::AppRenderContext context{catalog, snapshot};
    for (const cadenza::App* app : apps) {
      CAPTURE(app->name());
      cadenza::MonoFramebuffer previous{profile};
      cadenza::MonoFramebuffer current{profile};
      cadenza::MonoCanvas previousCanvas{previous};
      REQUIRE(app->renderLaunchFrame(previousCanvas, 0.0F, context));
      std::size_t maximumChanged = 0;
      for (int sample = 1; sample <= 12; ++sample) {
        cadenza::MonoCanvas currentCanvas{current};
        REQUIRE(app->renderLaunchFrame(
            currentCanvas, static_cast<float>(sample) / 12.0F, context));
        maximumChanged =
            std::max(maximumChanged, changedPixels(previous, current));
        previous = current;
      }
      CAPTURE(maximumChanged);
      const std::size_t pixels =
          static_cast<std::size_t>(previous.width()) * previous.height();
      CHECK(maximumChanged <= pixels / 5U);
    }
  }
}

TEST_CASE("Launcher input and launch never mutate Cover pixels") {
  cadenza::LauncherApp launcher;
  CoverProbeApp covered{"Covered"};
  cadenza::AppRuntime runtime{cadenza::FramebufferProfile::TEmbed,
                              cadenza::kCutTransition};
  cadenza::system::SystemServiceHost services;
  REQUIRE(registerBuiltin(runtime, cadenza::apps::kLauncherAppId, launcher,
                          false));
  REQUIRE(runtime.registerApp(cadenza::AppId{0x0201}, covered, true));
  REQUIRE(runtime.begin(cadenza::apps::kLauncherAppId));
  cadenza::MonoFramebuffer framebuffer{cadenza::FramebufferProfile::TEmbed};
  cadenza::MonoCanvas canvas{framebuffer};

  auto renderHash = [&]() {
    framebuffer.clear(false);
    cadenza::test::renderApp(launcher, canvas, runtime, services);
    return framebufferHash(framebuffer);
  };
  const std::uint64_t idleHash = renderHash();

  cadenza::InputFrame pressed;
  pressed.pressed = true;
  cadenza::test::updateApp(launcher, 0.0F, pressed, runtime, services);
  CHECK(renderHash() == idleHash);

  cadenza::InputFrame released;
  released.released = true;
  cadenza::test::updateApp(launcher, 0.0F, released, runtime, services);
  CHECK(renderHash() == idleHash);

  cadenza::InputFrame clicked;
  clicked.clicked = true;
  cadenza::test::updateApp(launcher, 0.0F, clicked, runtime, services);
  CHECK(runtime.transitioning());
  CHECK(renderHash() == idleHash);
}

TEST_CASE("Launcher clips moving Covers without changing their layout bounds") {
  cadenza::LauncherApp launcher;
  CoverProbeApp first{"First"};
  CoverProbeApp second{"Second"};
  CoverProbeApp third{"Third"};
  cadenza::AppRuntime runtime{cadenza::FramebufferProfile::TEmbed,
                              cadenza::kCutTransition};
  cadenza::system::SystemServiceHost services;
  REQUIRE(registerBuiltin(runtime, cadenza::apps::kLauncherAppId, launcher,
                          false));
  REQUIRE(runtime.registerApp(cadenza::AppId{0x0201}, first, true));
  REQUIRE(runtime.registerApp(cadenza::AppId{0x0202}, second, true));
  REQUIRE(runtime.registerApp(cadenza::AppId{0x0203}, third, true));
  REQUIRE(runtime.begin(cadenza::apps::kLauncherAppId));
  REQUIRE(services.submit(cadenza::SystemCommand::setLauncherOrientation(
      cadenza::LauncherOrientation::Horizontal)));
  services.commitCommands();
  cadenza::MonoFramebuffer framebuffer{cadenza::FramebufferProfile::TEmbed};
  cadenza::MonoCanvas canvas{framebuffer};

  cadenza::test::renderApp(launcher, canvas, runtime, services);
  cadenza::InputFrame turn;
  turn.turn = 1;
  cadenza::test::updateApp(launcher, 1.0F / 60.0F, turn, runtime, services);
  cadenza::test::renderApp(launcher, canvas, runtime, services);

  for (const CoverProbeApp* app : {&first, &second, &third}) {
    REQUIRE(app->renderCount > 0);
    CHECK(app->minimumWidth == app->maximumWidth);
  }
}

TEST_CASE("built-in Launcher Covers are distinct deterministic and bounded") {
  constexpr std::array<cadenza::AppId, 4> ids{
      cadenza::apps::kTimerAppId, cadenza::apps::kMotionAppId,
      cadenza::apps::kSettingsAppId, cadenza::apps::kGalleryAppId};
  for (const cadenza::FramebufferProfile profile : {
           cadenza::FramebufferProfile::TEmbed,
           cadenza::FramebufferProfile::Sharp}) {
    cadenza::LauncherApp launcher;
    cadenza::TimerApp timer;
    cadenza::MotionApp motion;
    cadenza::SettingsApp settings;
    cadenza::AnimationGalleryApp gallery;
    cadenza::AppRuntime runtime{profile, cadenza::kCutTransition};
    REQUIRE(registerBuiltin(runtime, cadenza::apps::kLauncherAppId, launcher,
                            false));
    REQUIRE(registerBuiltin(runtime, cadenza::apps::kTimerAppId, timer));
    REQUIRE(registerBuiltin(runtime, cadenza::apps::kMotionAppId, motion));
    REQUIRE(registerBuiltin(runtime, cadenza::apps::kSettingsAppId, settings));
    REQUIRE(registerBuiltin(runtime, cadenza::apps::kGalleryAppId, gallery));
    REQUIRE(runtime.begin(cadenza::apps::kLauncherAppId));
    const cadenza::AppCatalogView catalog = runtime.catalogView();
    std::array<std::uint64_t, 4> highlightedHashes{};
    for (std::size_t appIndex = 0; appIndex < ids.size(); ++appIndex) {
      std::uint64_t firstHash = 0;
      for (int pass = 0; pass < 2; ++pass) {
        TextDiagnosticSink diagnostics;
        cadenza::MonoFramebuffer framebuffer{profile};
        framebuffer.clear(true);
        cadenza::MonoCanvas canvas{framebuffer, &diagnostics};
        const bool tEmbed =
            profile == cadenza::FramebufferProfile::TEmbed;
        const cadenza::Rect bounds{13, 7, tEmbed ? 280 : 350,
                                   tEmbed ? 124 : 155};
        REQUIRE(catalog.renderLauncherCover(ids[appIndex], canvas, bounds));
        for (int y = 0; y < framebuffer.height(); ++y) {
          for (int x = 0; x < framebuffer.width(); ++x) {
            const bool outside = x < bounds.x || y < bounds.y ||
                x >= bounds.x + bounds.width ||
                y >= bounds.y + bounds.height;
            if (outside) CHECK(framebuffer.pixel(x, y));
          }
        }
        CHECK_FALSE(diagnostics.invalidGeometry);
        CHECK_FALSE(diagnostics.unexpectedGeometryClip);
        const std::uint64_t hash = framebufferHash(framebuffer);
        if (pass == 0) {
          firstHash = hash;
        } else {
          CHECK(hash == firstHash);
        }
      }
      highlightedHashes[appIndex] = firstHash;
    }
    for (std::size_t first = 0; first < highlightedHashes.size(); ++first) {
      for (std::size_t second = first + 1;
           second < highlightedHashes.size(); ++second) {
        CHECK(highlightedHashes[first] != highlightedHashes[second]);
      }
    }
  }
}

TEST_CASE("built-in Cover pixels do not depend on App lifecycle state") {
  cadenza::LauncherApp launcher;
  cadenza::TimerApp timer;
  cadenza::MotionApp motion;
  cadenza::SettingsApp settings;
  cadenza::AnimationGalleryApp gallery;
  cadenza::AppRuntime runtime{cadenza::FramebufferProfile::TEmbed,
                              cadenza::kCutTransition};
  REQUIRE(registerBuiltin(runtime, cadenza::apps::kLauncherAppId, launcher,
                          false));
  REQUIRE(registerBuiltin(runtime, cadenza::apps::kTimerAppId, timer));
  REQUIRE(registerBuiltin(runtime, cadenza::apps::kMotionAppId, motion));
  REQUIRE(registerBuiltin(runtime, cadenza::apps::kSettingsAppId, settings));
  REQUIRE(registerBuiltin(runtime, cadenza::apps::kGalleryAppId, gallery));
  REQUIRE(runtime.begin(cadenza::apps::kLauncherAppId));
  const cadenza::AppCatalogView catalog = runtime.catalogView();
  const cadenza::Rect bounds{20, 20, 280, 124};
  const std::array<cadenza::AppId, 4> ids{
      cadenza::apps::kTimerAppId, cadenza::apps::kMotionAppId,
      cadenza::apps::kSettingsAppId, cadenza::apps::kGalleryAppId};
  const std::array<cadenza::App*, 4> apps{
      &timer, &motion, &settings, &gallery};
  for (std::size_t index = 0; index < ids.size(); ++index) {
    const cadenza::AppId id = ids[index];
    cadenza::MonoFramebuffer before{cadenza::FramebufferProfile::TEmbed};
    cadenza::MonoFramebuffer after{cadenza::FramebufferProfile::TEmbed};
    cadenza::MonoCanvas beforeCanvas{before};
    cadenza::MonoCanvas afterCanvas{after};
    REQUIRE(catalog.renderLauncherCover(id, beforeCanvas, bounds));
    cadenza::App* app = apps[index];
    app->onEnter();
    cadenza::InputFrame input;
    input.turn = 1;
    input.clicked = true;
    cadenza::system::SystemServiceHost services;
    cadenza::test::updateApp(*app, 0.25F, input, runtime, services);
    REQUIRE(catalog.renderLauncherCover(id, afterCanvas, bounds));
    for (int y = bounds.y; y < bounds.y + bounds.height; ++y) {
      for (int x = bounds.x; x < bounds.x + bounds.width; ++x) {
        CHECK(before.pixel(x, y) == after.pixel(x, y));
      }
    }
  }
}

TEST_CASE("Launcher selection moves through a continuous unbounded track") {
  cadenza::LauncherApp launcher;
  NamedApp timer{"Timer"};
  NamedApp motion{"Motion"};
  NamedApp settings{"Settings"};
  NamedApp gallery{"Gallery"};
  cadenza::AppRuntime runtime;
  cadenza::system::SystemServiceHost services;
  registerNamedApps(runtime, launcher, timer, motion, settings, gallery);

  cadenza::InputFrame turn;
  turn.turn = 1;
  cadenza::test::updateApp(launcher, 1.0F / 60.0F, turn, runtime, services);
  CHECK(launcher.selectedIndex() == 1);
  CHECK(launcher.targetPosition() == 1);
  CHECK(launcher.visualPosition() > 0.0F);
  CHECK(launcher.visualPosition() < 1.0F);

  const float beforeRetarget = launcher.visualPosition();
  turn.turn = -1;
  cadenza::test::updateApp(launcher, 0.0F, turn, runtime, services);
  CHECK(launcher.selectedIndex() == 0);
  CHECK(launcher.targetPosition() == 0);
  CHECK(launcher.visualPosition() == doctest::Approx(beforeRetarget));
}

TEST_CASE("Launcher loop boundaries move one logical card in input direction") {
  cadenza::LauncherApp launcher;
  NamedApp timer{"Timer"};
  NamedApp motion{"Motion"};
  NamedApp settings{"Settings"};
  NamedApp gallery{"Gallery"};
  cadenza::AppRuntime runtime;
  cadenza::system::SystemServiceHost services;
  registerNamedApps(runtime, launcher, timer, motion, settings, gallery);

  cadenza::InputFrame toLast;
  toLast.turn = 3;
  cadenza::test::updateApp(launcher, 0.0F, toLast, runtime, services);
  CHECK(launcher.selectedIndex() == 3);
  CHECK(launcher.targetPosition() == 3);

  cadenza::InputFrame forward;
  forward.turn = 1;
  cadenza::test::updateApp(launcher, 0.0F, forward, runtime, services);
  CHECK(launcher.selectedIndex() == 0);
  CHECK(launcher.targetPosition() == 4);

  cadenza::InputFrame backward;
  backward.turn = -1;
  cadenza::test::updateApp(launcher, 0.0F, backward, runtime, services);
  CHECK(launcher.selectedIndex() == 3);
  CHECK(launcher.targetPosition() == 3);
}

TEST_CASE("Launcher opens the latest logical selection before motion settles") {
  cadenza::LauncherApp launcher;
  NamedApp timer{"Timer"};
  NamedApp motion{"Motion"};
  NamedApp settings{"Settings"};
  NamedApp gallery{"Gallery"};
  cadenza::AppRuntime runtime;
  cadenza::system::SystemServiceHost services;
  registerNamedApps(runtime, launcher, timer, motion, settings, gallery);

  cadenza::InputFrame turn;
  turn.turn = 1;
  cadenza::test::updateRuntime(runtime, services, 1.0F / 60.0F, turn);
  REQUIRE_FALSE(launcher.settled());
  cadenza::InputFrame click;
  click.clicked = true;
  cadenza::test::updateRuntime(runtime, services, 0.0F, click);
  REQUIRE(runtime.transitioning());
  cadenza::test::updateRuntime(runtime, services, 0.41F);
  CHECK(runtime.currentId() == cadenza::apps::kMotionAppId);
}

TEST_CASE("empty Launcher ignores navigation and open safely") {
  cadenza::LauncherApp launcher;
  cadenza::AppRuntime runtime;
  cadenza::system::SystemServiceHost services;
  REQUIRE(registerBuiltin(runtime, cadenza::apps::kLauncherAppId, launcher,
                          false));
  REQUIRE(runtime.begin(cadenza::apps::kLauncherAppId));

  cadenza::InputFrame input;
  input.turn = 12;
  input.clicked = true;
  cadenza::test::updateRuntime(runtime, services, 1.0F / 60.0F, input);
  CHECK_FALSE(runtime.transitioning());
  CHECK(launcher.selectedIndex() == 0);
  CHECK(launcher.targetPosition() == 0);
  CHECK(std::isfinite(launcher.visualPosition()));
}

TEST_CASE("Launcher motion profiles ease monotonically and settle exactly") {
  cadenza::LauncherApp launcher;
  NamedApp timer{"Timer"};
  NamedApp motion{"Motion"};
  NamedApp settings{"Settings"};
  NamedApp gallery{"Gallery"};
  cadenza::AppRuntime runtime;
  cadenza::system::SystemServiceHost services;
  registerNamedApps(runtime, launcher, timer, motion, settings, gallery);

  cadenza::InputFrame turn;
  turn.turn = 1;
  cadenza::test::updateApp(launcher, 1.0F / 60.0F, turn, runtime, services);
  float previous = launcher.visualPosition();
  CHECK(previous > 0.0F);
  CHECK(previous < 1.0F);
  int normalFrames = 1;
  while (!launcher.settled() && normalFrames < 120) {
    cadenza::test::updateApp(launcher, 1.0F / 60.0F, {}, runtime, services);
    CHECK(launcher.visualPosition() >= previous);
    CHECK(launcher.visualPosition() <= 1.0F);
    previous = launcher.visualPosition();
    ++normalFrames;
  }
  CHECK(normalFrames == 15);
  CHECK(launcher.settled());
  CHECK(launcher.visualPosition() == doctest::Approx(1.0F));

  REQUIRE(services.submit(cadenza::SystemCommand::setMotionProfile(
      cadenza::MotionProfile::Reduced)));
  services.commitCommands();
  cadenza::test::updateApp(launcher, 0.0F, {}, runtime, services);
  turn.turn = 1;
  cadenza::test::updateApp(launcher, 1.0F / 60.0F, turn, runtime, services);
  previous = launcher.visualPosition();
  CHECK(previous > 1.0F);
  CHECK(previous < 2.0F);
  int reducedFrames = 1;
  while (!launcher.settled() && reducedFrames < 120) {
    cadenza::test::updateApp(launcher, 1.0F / 60.0F, {}, runtime, services);
    CHECK(launcher.visualPosition() >= previous);
    CHECK(launcher.visualPosition() <= 2.0F);
    previous = launcher.visualPosition();
    ++reducedFrames;
  }
  CHECK(reducedFrames < normalFrames);
  CHECK(launcher.settled());
  CHECK(launcher.visualPosition() == doctest::Approx(2.0F));
}

TEST_CASE("Launcher reverse retarget never crosses either target") {
  cadenza::LauncherApp launcher;
  NamedApp clock{"Clock"};
  NamedApp motion{"Motion"};
  NamedApp settings{"Settings"};
  NamedApp gallery{"Gallery"};
  cadenza::AppRuntime runtime;
  cadenza::system::SystemServiceHost services;
  registerNamedApps(runtime, launcher, clock, motion, settings, gallery);

  cadenza::InputFrame turn;
  turn.turn = 1;
  cadenza::test::updateApp(launcher, 1.0F / 60.0F, turn, runtime, services);
  const float beforeReverse = launcher.visualPosition();
  REQUIRE(beforeReverse > 0.0F);
  REQUIRE(beforeReverse < 1.0F);

  turn.turn = -1;
  cadenza::test::updateApp(launcher, 0.0F, turn, runtime, services);
  CHECK(launcher.visualPosition() == doctest::Approx(beforeReverse));
  CHECK(launcher.targetPosition() == 0);

  float previous = beforeReverse;
  for (int frame = 0; frame < 120 && !launcher.settled(); ++frame) {
    cadenza::test::updateApp(launcher, 1.0F / 60.0F, {}, runtime, services);
    CHECK(launcher.visualPosition() >= 0.0F);
    CHECK(launcher.visualPosition() <= previous);
    previous = launcher.visualPosition();
  }
  CHECK(launcher.settled());
  CHECK(launcher.visualPosition() == doctest::Approx(0.0F));
}

TEST_CASE("Launcher motion profile switch and long-run rebase do not jump") {
  cadenza::LauncherApp launcher;
  NamedApp timer{"Timer"};
  NamedApp motion{"Motion"};
  NamedApp settings{"Settings"};
  NamedApp gallery{"Gallery"};
  cadenza::AppRuntime runtime;
  cadenza::system::SystemServiceHost services;
  registerNamedApps(runtime, launcher, timer, motion, settings, gallery);

  cadenza::InputFrame turn;
  turn.turn = 1;
  cadenza::test::updateApp(launcher, 1.0F / 60.0F, turn, runtime, services);
  const float beforeProfileSwitch = launcher.visualPosition();
  REQUIRE(services.submit(cadenza::SystemCommand::setMotionProfile(
      cadenza::MotionProfile::Reduced)));
  services.commitCommands();
  cadenza::test::updateApp(launcher, 0.0F, {}, runtime, services);
  CHECK(launcher.visualPosition() == doctest::Approx(beforeProfileSwitch));

  cadenza::InputFrame manyTurns;
  manyTurns.turn = 4096;
  cadenza::test::updateApp(launcher, 2.0F, manyTurns, runtime, services);
  for (int frame = 0; frame < 240 && !launcher.settled(); ++frame) {
    cadenza::test::updateApp(launcher, 1.0F / 60.0F, {}, runtime, services);
  }
  CHECK(launcher.settled());
  CHECK(launcher.selectedIndex() == 1);
  CHECK(launcher.targetPosition() == 1);
  CHECK(launcher.visualPosition() == doctest::Approx(1.0F));
}

TEST_CASE("one input frame emits at most one semantic navigation cue") {
  cadenza::LauncherApp launcher;
  NamedApp timer{"Timer"};
  NamedApp motion{"Motion"};
  NamedApp settings{"Settings"};
  NamedApp gallery{"Gallery"};
  cadenza::AppRuntime runtime;
    cadenza::system::SystemServiceHost services;
  registerNamedApps(runtime, launcher, timer, motion, settings, gallery);

  cadenza::InputFrame turn;
  turn.turn = 7;
  cadenza::test::updateRuntime(runtime, services, 1.0F / 60.0F, turn);
  CHECK(services.sound().pendingCommandCount() == 1);
  CHECK(services.sound().lastAcceptedCue() ==
        cadenza::audio::SoundCue::Navigate);
}

TEST_CASE("bundled Apps emit success and boundary cues from actual state") {
  cadenza::AppRuntime runtime;
    cadenza::system::SystemServiceHost services;
  cadenza::LauncherApp launcher;
  cadenza::TimerApp timer;
  cadenza::MotionApp motion;
  cadenza::SettingsApp settings;
  REQUIRE(registerBuiltin(runtime, cadenza::apps::kLauncherAppId, launcher, false));
  REQUIRE(registerBuiltin(runtime, cadenza::apps::kTimerAppId, timer));
  REQUIRE(registerBuiltin(runtime, cadenza::apps::kMotionAppId, motion));
  REQUIRE(registerBuiltin(runtime, cadenza::apps::kSettingsAppId, settings));
  REQUIRE(runtime.begin(cadenza::apps::kLauncherAppId));

  cadenza::InputFrame click;
  click.clicked = true;
  cadenza::test::updateApp(timer, 0.0F, click, runtime, services,
                           cadenza::apps::kTimerAppId);
  CHECK(services.sound().lastAcceptedCue() ==
        cadenza::audio::SoundCue::ToggleOn);

  cadenza::InputFrame largeTurn;
  largeTurn.turn = 100;
  cadenza::test::updateApp(motion, 0.0F, largeTurn, runtime, services,
                           cadenza::apps::kMotionAppId);
  CHECK(services.sound().lastAcceptedCue() ==
        cadenza::audio::SoundCue::Navigate);
  services.sound().advance(0.03F);
  cadenza::InputFrame boundaryTurn;
  boundaryTurn.turn = 1;
  cadenza::test::updateApp(motion, 0.0F, boundaryTurn, runtime, services,
                           cadenza::apps::kMotionAppId);
  CHECK(services.sound().lastAcceptedCue() ==
        cadenza::audio::SoundCue::Boundary);
}

TEST_CASE("Activation Timer uses turn to choose minutes and click to start") {
  cadenza::AppRuntime runtime;
  cadenza::system::SystemServiceHost services;
  cadenza::LauncherApp launcher;
  cadenza::TimerApp timer;
  REQUIRE(registerBuiltin(runtime, cadenza::apps::kLauncherAppId, launcher,
                          false));
  REQUIRE(registerBuiltin(runtime, cadenza::apps::kTimerAppId, timer));
  REQUIRE(runtime.begin(cadenza::apps::kLauncherAppId));
  timer.onEnter();

  cadenza::InputFrame turn;
  turn.turn = 3;
  cadenza::test::updateApp(timer, 0.0F, turn, runtime, services,
                           cadenza::apps::kTimerAppId);
  CHECK(services.snapshot().timer.state == cadenza::TimerState::Ready);
  CHECK(services.sound().lastAcceptedCue() ==
        cadenza::audio::SoundCue::Navigate);

  cadenza::InputFrame click;
  click.clicked = true;
  cadenza::test::updateApp(timer, 0.0F, click, runtime, services,
                           cadenza::apps::kTimerAppId);
  CHECK(services.snapshot().timer.state == cadenza::TimerState::Running);
  CHECK(services.snapshot().timer.configuredDurationMs == 13 * 60000);
  CHECK(services.snapshot().timer.owner == cadenza::apps::kTimerAppId);
}

TEST_CASE("Activation Timer wraps Ready duration between one and 99") {
  cadenza::AppRuntime runtime;
  cadenza::system::SystemServiceHost services;
  cadenza::TimerApp timer;
  REQUIRE(registerBuiltin(runtime, cadenza::apps::kTimerAppId, timer));
  REQUIRE(runtime.begin(cadenza::apps::kTimerAppId));

  cadenza::InputFrame turn;
  turn.turn = 89;
  cadenza::test::updateApp(timer, 0.0F, turn, runtime, services,
                           cadenza::apps::kTimerAppId);
  turn.turn = 1;
  cadenza::test::updateApp(timer, 0.0F, turn, runtime, services,
                           cadenza::apps::kTimerAppId);
  turn.turn = -1;
  cadenza::test::updateApp(timer, 0.0F, turn, runtime, services,
                           cadenza::apps::kTimerAppId);

  cadenza::InputFrame click;
  click.clicked = true;
  cadenza::test::updateApp(timer, 0.0F, click, runtime, services,
                           cadenza::apps::kTimerAppId);
  CHECK(services.snapshot().timer.state == cadenza::TimerState::Running);
  CHECK(services.snapshot().timer.configuredDurationMs == 99 * 60000);
}

TEST_CASE("Activation Timer can adjust a paused sub-minute remainder") {
  cadenza::AppRuntime runtime;
  cadenza::system::SystemServiceHost services;
  cadenza::TimerApp timer;
  REQUIRE(registerBuiltin(runtime, cadenza::apps::kTimerAppId, timer));
  REQUIRE(runtime.begin(cadenza::apps::kTimerAppId));

  cadenza::InputFrame turn;
  turn.turn = -9;
  cadenza::test::updateApp(timer, 0.0F, turn, runtime, services,
                           cadenza::apps::kTimerAppId);
  cadenza::InputFrame click;
  click.clicked = true;
  cadenza::test::updateApp(timer, 0.0F, click, runtime, services,
                           cadenza::apps::kTimerAppId);
  services.beginFrame(42.0F);
  cadenza::test::updateApp(timer, 0.0F, click, runtime, services,
                           cadenza::apps::kTimerAppId);
  REQUIRE(services.snapshot().timer.remainingMs == 18000);

  turn.turn = 1;
  cadenza::test::updateApp(timer, 0.0F, turn, runtime, services,
                           cadenza::apps::kTimerAppId);
  CHECK(services.snapshot().timer.remainingMs == 1 * 60000);
}

TEST_CASE("Activation Timer pauses resets seconds when adjusting minutes and resumes") {
  cadenza::AppRuntime runtime;
  cadenza::system::SystemServiceHost services;
  cadenza::LauncherApp launcher;
  cadenza::TimerApp timer;
  REQUIRE(registerBuiltin(runtime, cadenza::apps::kLauncherAppId, launcher,
                          false));
  REQUIRE(registerBuiltin(runtime, cadenza::apps::kTimerAppId, timer));
  REQUIRE(runtime.begin(cadenza::apps::kLauncherAppId));

  cadenza::InputFrame click;
  click.clicked = true;
  cadenza::test::updateApp(timer, 0.0F, click, runtime, services,
                           cadenza::apps::kTimerAppId);
  services.beginFrame(42.0F);

  cadenza::InputFrame runningTurn;
  runningTurn.turn = 5;
  const auto beforeTurn = services.snapshot().timer.remainingMs;
  cadenza::test::updateApp(timer, 0.0F, runningTurn, runtime, services,
                           cadenza::apps::kTimerAppId);
  CHECK(services.snapshot().timer.remainingMs == beforeTurn);
  CHECK(services.sound().lastAcceptedCue() ==
        cadenza::audio::SoundCue::Boundary);

  cadenza::test::updateApp(timer, 0.0F, click, runtime, services,
                           cadenza::apps::kTimerAppId);
  REQUIRE(services.snapshot().timer.state == cadenza::TimerState::Paused);
  REQUIRE(services.snapshot().timer.remainingMs == 9 * 60000 + 18000);

  cadenza::InputFrame adjust;
  adjust.turn = 2;
  cadenza::test::updateApp(timer, 0.0F, adjust, runtime, services,
                           cadenza::apps::kTimerAppId);
  CHECK(services.snapshot().timer.remainingMs == 11 * 60000);
  CHECK(services.snapshot().timer.configuredDurationMs == 11 * 60000);
  adjust.turn = 88;
  cadenza::test::updateApp(timer, 0.0F, adjust, runtime, services,
                           cadenza::apps::kTimerAppId);
  CHECK(services.snapshot().timer.remainingMs == 99 * 60000);
  adjust.turn = 1;
  cadenza::test::updateApp(timer, 0.0F, adjust, runtime, services,
                           cadenza::apps::kTimerAppId);
  CHECK(services.snapshot().timer.remainingMs == 1 * 60000);
  cadenza::test::updateApp(timer, 0.0F, click, runtime, services,
                           cadenza::apps::kTimerAppId);
  CHECK(services.snapshot().timer.state == cadenza::TimerState::Running);
}

TEST_CASE("Timer state badge has equal optical vertical padding") {
  for (const auto profile : {cadenza::FramebufferProfile::TEmbed,
                             cadenza::FramebufferProfile::Sharp}) {
    CAPTURE(static_cast<int>(profile));
    cadenza::AppRuntime runtime{profile, cadenza::kCutTransition};
    cadenza::system::SystemServiceHost services;
    cadenza::TimerApp timer;
    REQUIRE(registerBuiltin(runtime, cadenza::apps::kTimerAppId, timer));
    REQUIRE(runtime.begin(cadenza::apps::kTimerAppId));

    cadenza::InputFrame click;
    click.clicked = true;
    cadenza::test::updateApp(timer, 0.0F, click, runtime, services,
                             cadenza::apps::kTimerAppId);
    cadenza::test::updateApp(timer, 0.0F, click, runtime, services,
                             cadenza::apps::kTimerAppId);
    REQUIRE(services.snapshot().timer.state == cadenza::TimerState::Paused);

    cadenza::MonoFramebuffer frame{profile};
    cadenza::MonoCanvas canvas{frame};
    cadenza::test::renderApp(timer, canvas, runtime, services);

    constexpr int kBadgeTop = 2;
    const int badgeRight = frame.width() - 13;
    int badgeLeft = badgeRight;
    while (badgeLeft > 0 && frame.pixel(badgeLeft - 1, kBadgeTop + 3)) {
      --badgeLeft;
    }
    const int badgeWidth = badgeRight - badgeLeft + 1;
    const int probeX = badgeLeft + 4;
    int badgeBottom = kBadgeTop;
    while (badgeBottom + 1 < frame.height() &&
           frame.pixel(probeX, badgeBottom + 1)) {
      ++badgeBottom;
    }

    int firstInkRow = badgeBottom + 1;
    int lastInkRow = kBadgeTop - 1;
    for (int y = kBadgeTop; y <= badgeBottom; ++y) {
      for (int x = badgeLeft + 4; x < badgeLeft + badgeWidth - 4; ++x) {
        if (frame.pixel(x, y)) continue;
        firstInkRow = std::min(firstInkRow, y);
        lastInkRow = std::max(lastInkRow, y);
      }
    }
    REQUIRE(lastInkRow >= firstInkRow);
    CHECK(firstInkRow - kBadgeTop == badgeBottom - lastInkRow);
  }
}

TEST_CASE("Timer presentation feedback has deterministic lifecycle and clears on handoff") {
  cadenza::AppRuntime runtime;
  cadenza::system::SystemServiceHost services;
  cadenza::LauncherApp launcher;
  cadenza::TimerApp timer;
  REQUIRE(registerBuiltin(runtime, cadenza::apps::kLauncherAppId, launcher,
                          false));
  REQUIRE(registerBuiltin(runtime, cadenza::apps::kTimerAppId, timer));
  REQUIRE(runtime.begin(cadenza::apps::kTimerAppId));

  cadenza::InputFrame click;
  click.clicked = true;
  cadenza::test::updateApp(timer, 0.0F, click, runtime, services,
                           cadenza::apps::kTimerAppId);
  CHECK(timer.presentationState() ==
        cadenza::TimerPresentationState::Starting);
  CHECK(timer.presentationElapsed() == doctest::Approx(0.0F));

  cadenza::MonoFramebuffer first{cadenza::FramebufferProfile::TEmbed};
  cadenza::MonoFramebuffer middle{cadenza::FramebufferProfile::TEmbed};
  cadenza::MonoCanvas firstCanvas{first};
  cadenza::MonoCanvas middleCanvas{middle};
  cadenza::test::renderApp(timer, firstCanvas, runtime, services);
  cadenza::test::updateApp(timer, 0.12F, {}, runtime, services,
                           cadenza::apps::kTimerAppId);
  cadenza::test::renderApp(timer, middleCanvas, runtime, services);
  CHECK(framebufferHash(first) != framebufferHash(middle));
  CHECK(timer.presentationElapsed() == doctest::Approx(0.12F));

  timer.onExit();
  CHECK(timer.presentationState() == cadenza::TimerPresentationState::None);
  CHECK(timer.presentationElapsed() == doctest::Approx(0.0F));
  timer.onEnter();
  CHECK(timer.presentationState() == cadenza::TimerPresentationState::None);

  cadenza::test::updateApp(timer, 0.0F, click, runtime, services,
                           cadenza::apps::kTimerAppId);
  CHECK(timer.presentationState() ==
        cadenza::TimerPresentationState::Pausing);
  cadenza::test::updateApp(timer, 0.18F, {}, runtime, services,
                           cadenza::apps::kTimerAppId);
  CHECK(timer.presentationState() == cadenza::TimerPresentationState::None);

  cadenza::test::updateApp(timer, 0.0F, click, runtime, services,
                           cadenza::apps::kTimerAppId);
  CHECK(timer.presentationState() ==
        cadenza::TimerPresentationState::Resuming);
}

TEST_CASE("Timer feedback keyframes preserve direction on both profiles") {
  for (const auto profile : {cadenza::FramebufferProfile::TEmbed,
                             cadenza::FramebufferProfile::Sharp}) {
    CAPTURE(static_cast<int>(profile));
    cadenza::AppRuntime runtime{profile, cadenza::kCutTransition};
    cadenza::system::SystemServiceHost services;
    cadenza::TimerApp timer;
    REQUIRE(registerBuiltin(runtime, cadenza::apps::kTimerAppId, timer));
    REQUIRE(runtime.begin(cadenza::apps::kTimerAppId));

    const cadenza::Rect presentationRegion{
        0, profile == cadenza::FramebufferProfile::Sharp ? 39 : 25,
        runtime.canvasWidth(),
        profile == cadenza::FramebufferProfile::Sharp ? 140 : 105};
    const auto render = [&]() {
      cadenza::MonoFramebuffer frame{profile};
      cadenza::MonoCanvas canvas{frame};
      cadenza::test::renderApp(timer, canvas, runtime, services);
      return frame;
    };
    cadenza::InputFrame click;
    click.clicked = true;

    cadenza::test::updateApp(timer, 0.0F, click, runtime, services,
                             cadenza::apps::kTimerAppId);
    REQUIRE(timer.presentationState() ==
            cadenza::TimerPresentationState::Starting);
    const auto startingFirst = render();
    cadenza::test::updateApp(timer, 0.12F, {}, runtime, services,
                             cadenza::apps::kTimerAppId);
    const auto startingMiddle = render();
    cadenza::test::updateApp(timer, 0.12F, {}, runtime, services,
                             cadenza::apps::kTimerAppId);
    const auto runningStable = render();
    REQUIRE(timer.presentationState() == cadenza::TimerPresentationState::None);
    const auto startingFirstDelta = changedBoundsIn(
        startingFirst, runningStable, presentationRegion);
    const auto startingMiddleDelta = changedBoundsIn(
        startingMiddle, runningStable, presentationRegion);
    REQUIRE(startingFirstDelta.width > 0);
    REQUIRE(startingMiddleDelta.width > 0);
    CHECK(startingFirstDelta.x < startingMiddleDelta.x);
    CHECK(services.sound().lastAcceptedCue() ==
          cadenza::audio::SoundCue::ToggleOn);

    cadenza::test::updateApp(timer, 0.0F, click, runtime, services,
                             cadenza::apps::kTimerAppId);
    REQUIRE(timer.presentationState() ==
            cadenza::TimerPresentationState::Pausing);
    const auto pausingFirst = render();
    cadenza::test::updateApp(timer, 0.09F, {}, runtime, services,
                             cadenza::apps::kTimerAppId);
    const auto pausingMiddle = render();
    cadenza::test::updateApp(timer, 0.09F, {}, runtime, services,
                             cadenza::apps::kTimerAppId);
    const auto pausedStable = render();
    REQUIRE(timer.presentationState() == cadenza::TimerPresentationState::None);
    const auto pausingFirstDelta = changedBoundsIn(
        pausingFirst, pausedStable, presentationRegion);
    const auto pausingMiddleDelta = changedBoundsIn(
        pausingMiddle, pausedStable, presentationRegion);
    REQUIRE(pausingFirstDelta.width > 0);
    REQUIRE(pausingMiddleDelta.width > 0);
    CHECK(pausingFirstDelta.x > pausingMiddleDelta.x);
    CHECK(services.sound().lastAcceptedCue() ==
          cadenza::audio::SoundCue::ToggleOff);

    cadenza::test::updateApp(timer, 0.0F, click, runtime, services,
                             cadenza::apps::kTimerAppId);
    REQUIRE(timer.presentationState() ==
            cadenza::TimerPresentationState::Resuming);
    const auto resumingFirst = render();
    cadenza::test::updateApp(timer, 0.09F, {}, runtime, services,
                             cadenza::apps::kTimerAppId);
    const auto resumingMiddle = render();
    cadenza::test::updateApp(timer, 0.09F, {}, runtime, services,
                             cadenza::apps::kTimerAppId);
    const auto resumedStable = render();
    REQUIRE(timer.presentationState() == cadenza::TimerPresentationState::None);
    const auto resumingFirstDelta = changedBoundsIn(
        resumingFirst, resumedStable, presentationRegion);
    const auto resumingMiddleDelta = changedBoundsIn(
        resumingMiddle, resumedStable, presentationRegion);
    REQUIRE(resumingFirstDelta.width > 0);
    REQUIRE(resumingMiddleDelta.width > 0);
    CHECK(resumingFirstDelta.x < resumingMiddleDelta.x);
    CHECK(services.sound().lastAcceptedCue() ==
          cadenza::audio::SoundCue::ToggleOn);
  }
}

TEST_CASE("Reduced Motion Timer feedback is static and ends after 100 ms") {
  for (const auto profile : {cadenza::FramebufferProfile::TEmbed,
                             cadenza::FramebufferProfile::Sharp}) {
    cadenza::AppRuntime runtime{profile, cadenza::kCutTransition};
    cadenza::system::SystemServiceHost services;
    cadenza::TimerApp timer;
    REQUIRE(registerBuiltin(runtime, cadenza::apps::kTimerAppId, timer));
    REQUIRE(runtime.begin(cadenza::apps::kTimerAppId));
    REQUIRE(services.submit(cadenza::SystemCommand::setMotionProfile(
        cadenza::MotionProfile::Reduced)));
    services.commitCommands();

    const auto render = [&]() {
      cadenza::MonoFramebuffer frame{profile};
      cadenza::MonoCanvas canvas{frame};
      cadenza::test::renderApp(timer, canvas, runtime, services);
      return frame;
    };
    cadenza::InputFrame click;
    click.clicked = true;
    cadenza::test::updateApp(timer, 0.0F, click, runtime, services,
                             cadenza::apps::kTimerAppId);
    const cadenza::Rect presentationRegion{
        0, profile == cadenza::FramebufferProfile::Sharp ? 39 : 25,
        runtime.canvasWidth(),
        profile == cadenza::FramebufferProfile::Sharp ? 140 : 105};
    const auto first = render();
    cadenza::test::updateApp(timer, 0.05F, {}, runtime, services,
                             cadenza::apps::kTimerAppId);
    const auto middle = render();
    CHECK(changedBoundsIn(first, middle, presentationRegion).width == 0);
    cadenza::test::updateApp(timer, 0.05F, {}, runtime, services,
                             cadenza::apps::kTimerAppId);
    const auto stable = render();
    CHECK(timer.presentationState() == cadenza::TimerPresentationState::None);
    CHECK(changedBoundsIn(first, stable, presentationRegion).width > 0);
  }
}

TEST_CASE("Expired Activation Timer ignores App input and survives App handoff") {
  cadenza::AppRuntime runtime{cadenza::FramebufferProfile::TEmbed,
                              cadenza::kCutTransition};
  cadenza::system::SystemServiceHost services;
  cadenza::LauncherApp launcher;
  cadenza::TimerApp timer;
  cadenza::MotionApp motion;
  REQUIRE(registerBuiltin(runtime, cadenza::apps::kLauncherAppId, launcher,
                          false));
  REQUIRE(registerBuiltin(runtime, cadenza::apps::kTimerAppId, timer));
  REQUIRE(registerBuiltin(runtime, cadenza::apps::kMotionAppId, motion));
  REQUIRE(runtime.begin(cadenza::apps::kTimerAppId));

  cadenza::InputFrame click;
  click.clicked = true;
  cadenza::test::updateApp(timer, 0.0F, click, runtime, services,
                           cadenza::apps::kTimerAppId);
  REQUIRE(runtime.open(cadenza::apps::kMotionAppId));
  runtime.updateWithSystem(1.0F, {}, services.snapshot(), services);
  CHECK(services.snapshot().timer.state == cadenza::TimerState::Running);
  services.beginFrame(600.0F);
  REQUIRE(services.snapshot().timer.state == cadenza::TimerState::Expired);

  cadenza::InputFrame noisy;
  noisy.clicked = true;
  noisy.turn = 8;
  cadenza::test::updateApp(timer, 0.0F, noisy, runtime, services,
                           cadenza::apps::kTimerAppId);
  CHECK(services.snapshot().timer.state == cadenza::TimerState::Expired);
}

TEST_CASE("Settings exposes a sound row and cycles session volume") {
  cadenza::AppRuntime runtime;
    cadenza::system::SystemServiceHost services;
  cadenza::SettingsApp settings;
  cadenza::LauncherApp launcher;
  REQUIRE(registerBuiltin(runtime, cadenza::apps::kLauncherAppId, launcher, false));
  REQUIRE(registerBuiltin(runtime, cadenza::apps::kSettingsAppId, settings));
  REQUIRE(runtime.begin(cadenza::apps::kSettingsAppId));

  cadenza::InputFrame selectSound;
  selectSound.turn = 1;
  cadenza::test::updateApp(settings, 0.03F, selectSound, runtime, services,
                           cadenza::apps::kSettingsAppId);
  cadenza::InputFrame click;
  click.clicked = true;
  cadenza::test::updateApp(settings, 0.0F, click, runtime, services,
                           cadenza::apps::kSettingsAppId);
  CHECK(services.snapshot().soundVolume == cadenza::audio::SoundVolume::High);
  cadenza::test::updateApp(settings, 0.0F, click, runtime, services,
                           cadenza::apps::kSettingsAppId);
  CHECK(services.snapshot().soundVolume == cadenza::audio::SoundVolume::Muted);
  cadenza::test::updateApp(settings, 0.0F, click, runtime, services,
                           cadenza::apps::kSettingsAppId);
  CHECK(services.snapshot().soundVolume == cadenza::audio::SoundVolume::Low);
}

TEST_CASE("Settings volume changes are immediately visible and muted stays visual") {
  for (const cadenza::FramebufferProfile profile : {
           cadenza::FramebufferProfile::TEmbed,
           cadenza::FramebufferProfile::Sharp}) {
    CAPTURE(static_cast<int>(profile));
    cadenza::AppRuntime runtime{profile};
    cadenza::system::SystemServiceHost services;
    cadenza::SettingsApp settings;
    cadenza::LauncherApp launcher;
    REQUIRE(registerBuiltin(runtime, cadenza::apps::kLauncherAppId, launcher, false));
    REQUIRE(registerBuiltin(runtime, cadenza::apps::kSettingsAppId, settings));
    REQUIRE(runtime.begin(cadenza::apps::kSettingsAppId));
    cadenza::InputFrame selectSound;
    selectSound.turn = 1;
    cadenza::test::updateApp(settings, 0.03F, selectSound, runtime, services,
                             cadenza::apps::kSettingsAppId);

    cadenza::MonoFramebuffer framebuffer{profile};
    cadenza::MonoCanvas canvas{framebuffer};
    cadenza::test::renderApp(settings, canvas, runtime, services);
    const std::vector<std::uint8_t> medium(
        framebuffer.data(), framebuffer.data() + framebuffer.sizeBytes());

    cadenza::InputFrame click;
    click.clicked = true;
    cadenza::test::updateApp(settings, 0.0F, click, runtime, services,
                             cadenza::apps::kSettingsAppId);
    cadenza::test::renderApp(settings, canvas, runtime, services);
    const std::vector<std::uint8_t> high(
        framebuffer.data(), framebuffer.data() + framebuffer.sizeBytes());
    CHECK(services.snapshot().soundVolume == cadenza::audio::SoundVolume::High);
    CHECK(high != medium);

    cadenza::test::updateApp(settings, 0.0F, click, runtime, services,
                             cadenza::apps::kSettingsAppId);
    cadenza::test::renderApp(settings, canvas, runtime, services);
    const std::vector<std::uint8_t> muted(
        framebuffer.data(), framebuffer.data() + framebuffer.sizeBytes());
    CHECK(services.snapshot().soundVolume == cadenza::audio::SoundVolume::Muted);
    CHECK(muted != high);
    std::array<std::int16_t, 256> samples{};
    services.renderAudio(samples.data(), samples.size());
    CHECK(std::all_of(samples.begin(), samples.end(),
                      [](std::int16_t sample) { return sample == 0; }));
    CHECK(hasBlackPixel(framebuffer));
  }
}

TEST_CASE("Settings switches Launcher orientation immediately at both profiles") {
  for (const cadenza::FramebufferProfile profile : {
           cadenza::FramebufferProfile::TEmbed,
           cadenza::FramebufferProfile::Sharp}) {
    CAPTURE(static_cast<int>(profile));
    cadenza::AppRuntime runtime{profile, cadenza::kCutTransition};
    cadenza::system::SystemServiceHost services;
    cadenza::SettingsApp settings;
    cadenza::LauncherApp launcher;
    REQUIRE(registerBuiltin(runtime, cadenza::apps::kLauncherAppId, launcher,
                            false));
    REQUIRE(registerBuiltin(runtime, cadenza::apps::kSettingsAppId, settings));
    REQUIRE(runtime.begin(cadenza::apps::kSettingsAppId));

    cadenza::InputFrame selectLauncher;
    selectLauncher.turn = 5;
    cadenza::test::updateApp(settings, 0.0F, selectLauncher, runtime, services,
                             cadenza::apps::kSettingsAppId);
    cadenza::InputFrame click;
    click.clicked = true;
    cadenza::test::updateApp(settings, 0.0F, click, runtime, services,
                             cadenza::apps::kSettingsAppId);
    CHECK(services.snapshot().launcherOrientation ==
          cadenza::LauncherOrientation::Horizontal);
    CHECK(services.sound().lastAcceptedCue() ==
          cadenza::audio::SoundCue::ToggleOn);

    TextDiagnosticSink diagnostics;
    cadenza::MonoFramebuffer framebuffer{profile};
    cadenza::MonoCanvas canvas{framebuffer, &diagnostics};
    cadenza::test::renderApp(settings, canvas, runtime, services);
    CHECK(hasBlackPixel(framebuffer));
    CHECK_FALSE(diagnostics.textClipped);

    cadenza::test::updateApp(settings, 0.0F, click, runtime, services,
                             cadenza::apps::kSettingsAppId);
    CHECK(services.snapshot().launcherOrientation ==
          cadenza::LauncherOrientation::Vertical);
    CHECK(services.sound().lastAcceptedCue() ==
          cadenza::audio::SoundCue::ToggleOff);
  }
}

bool hasWideBlackBand(const cadenza::MonoFramebuffer& framebuffer, int x0,
                      int x1, int y0, int y1) {
  const int span = std::max(1, x1 - x0);
  for (int y = std::max(0, y0);
       y < std::min<int>(framebuffer.height(), y1); ++y) {
    int ink = 0;
    for (int x = std::max(0, x0);
         x < std::min<int>(framebuffer.width(), x1); ++x) {
      if (framebuffer.pixel(x, y)) ++ink;
    }
    if (ink * 4 >= span * 3) return true;
  }
  return false;
}

TEST_CASE("Settings keeps the last item fully visible and opens About") {
  for (const cadenza::FramebufferProfile profile : {
           cadenza::FramebufferProfile::TEmbed,
           cadenza::FramebufferProfile::Sharp}) {
    CAPTURE(static_cast<int>(profile));
    cadenza::AppRuntime runtime{profile, cadenza::kCutTransition};
    cadenza::system::SystemServiceHost services;
    cadenza::SettingsApp settings;
    cadenza::LauncherApp launcher;
    REQUIRE(registerBuiltin(runtime, cadenza::apps::kLauncherAppId, launcher,
                            false));
    REQUIRE(registerBuiltin(runtime, cadenza::apps::kSettingsAppId, settings));
    REQUIRE(runtime.begin(cadenza::apps::kSettingsAppId));

    cadenza::MonoFramebuffer framebuffer{profile};
    cadenza::MonoCanvas canvas{framebuffer};
    cadenza::test::renderApp(settings, canvas, runtime, services);
    const std::uint64_t settingsHash = framebufferHash(framebuffer);
    const int titleWidth = static_cast<int>(
        canvas.measureText("SETTINGS", cadenza::TextRole::Title).width);
    const int panelMinimum = 12 + titleWidth + 4;
    const int panelMaximum = std::min(
        framebuffer.width() - 128,
        std::max(panelMinimum, framebuffer.width() * 30 / 100 + 24));
    const int rowsLeft = panelMaximum + 8;

    cadenza::InputFrame selectAbout;
    selectAbout.turn = 6;
    cadenza::test::updateApp(settings, 0.0F, selectAbout, runtime, services,
                             cadenza::apps::kSettingsAppId);
    CHECK(settings.selectedIndex() == 6);
    if (profile == cadenza::FramebufferProfile::TEmbed) {
      CHECK(settings.scrollOffset() > 0);
    }
    cadenza::test::renderApp(settings, canvas, runtime, services);
    CHECK(hasWideBlackBand(framebuffer, rowsLeft, framebuffer.width() - 12, 4,
                           framebuffer.height() - 16));

    cadenza::InputFrame click;
    click.clicked = true;
    cadenza::test::updateApp(settings, 0.0F, click, runtime, services,
                             cadenza::apps::kSettingsAppId);
    CHECK(settings.showingAbout());
    CHECK(services.sound().lastAcceptedCue() ==
          cadenza::audio::SoundCue::Confirm);

    TextDiagnosticSink diagnostics;
    cadenza::MonoCanvas aboutCanvas{framebuffer, &diagnostics};
    cadenza::test::renderApp(settings, aboutCanvas, runtime, services);
    CHECK(framebufferHash(framebuffer) != settingsHash);
    CHECK(hasBlackPixel(framebuffer));
    const int logoHeight =
        profile == cadenza::FramebufferProfile::TEmbed ? 124 : 155;
    CHECK(hasBlackInRect(framebuffer,
                         {0, 0, framebuffer.width(), logoHeight}));
    CHECK(hasBlackInRect(
        framebuffer,
        {0, logoHeight, framebuffer.width(),
         static_cast<int>(framebuffer.height()) - logoHeight}));
    CHECK_FALSE(diagnostics.textClipped);
    CHECK_FALSE(diagnostics.unexpectedGeometryClip);
    CHECK_FALSE(diagnostics.invalidGeometry);

    cadenza::test::updateApp(settings, 0.0F, click, runtime, services,
                             cadenza::apps::kSettingsAppId);
    CHECK_FALSE(settings.showingAbout());
    CHECK(services.sound().lastAcceptedCue() ==
          cadenza::audio::SoundCue::Back);
  }
}

TEST_CASE("Settings drives Wi-Fi and owner-bound provisioning without credentials") {
  cadenza::AppRuntime runtime;
  cadenza::system::SystemServiceHost services;
  cadenza::SettingsApp settings;
  cadenza::LauncherApp launcher;
  REQUIRE(registerBuiltin(runtime, cadenza::apps::kLauncherAppId, launcher,
                          false));
  REQUIRE(registerBuiltin(runtime, cadenza::apps::kSettingsAppId, settings));
  REQUIRE(runtime.begin(cadenza::apps::kSettingsAppId));
  services.connectivityService().setWiFiAvailable(true);

  cadenza::InputFrame selectWifi;
  selectWifi.turn = 3;
  cadenza::test::updateApp(settings, 0.0F, selectWifi, runtime, services,
                           cadenza::apps::kSettingsAppId);
  cadenza::InputFrame click;
  click.clicked = true;
  cadenza::test::updateApp(settings, 0.0F, click, runtime, services,
                           cadenza::apps::kSettingsAppId);
  CHECK(services.snapshot().connectivity.wifi.desired ==
        cadenza::WiFiDesiredPolicy::OnlineRequested);

  cadenza::InputFrame selectSetup;
  selectSetup.turn = 1;
  cadenza::test::updateApp(settings, 0.0F, selectSetup, runtime, services,
                           cadenza::apps::kSettingsAppId);
  cadenza::test::updateApp(settings, 0.0F, click, runtime, services,
                           cadenza::apps::kSettingsAppId);
  CHECK(services.snapshot().connectivity.provisioning.state ==
        cadenza::ProvisioningState::Advertising);
  CHECK(services.leases().ownerCount(
            cadenza::system::SystemResource::ProvisioningSession) == 1);

  cadenza::test::updateApp(settings, 0.0F, click, runtime, services,
                           cadenza::apps::kSettingsAppId);
  CHECK(services.snapshot().connectivity.provisioning.state ==
        cadenza::ProvisioningState::Stopping);
  const std::uint32_t cancelledGeneration =
      services.snapshot().connectivity.provisioning.generation;
  cadenza::system::ConnectivityAction action;
  while (services.connectivityService().tryPopAction(action)) {}
  REQUIRE(services.postPlatformEvent(
      cadenza::system::PlatformEvent::provisioningStopped(
          cancelledGeneration)));
  services.beginFrame(0.0F);
  cadenza::test::updateApp(settings, 0.0F, click, runtime, services,
                           cadenza::apps::kSettingsAppId);
  CHECK(services.snapshot().connectivity.provisioning.generation ==
        cancelledGeneration);
  CHECK_FALSE(services.connectivityService().tryPopAction(action));
  cadenza::test::updateApp(settings, 0.0F, click, runtime, services,
                           cadenza::apps::kSettingsAppId);
  CHECK(services.snapshot().connectivity.provisioning.generation !=
        cancelledGeneration);
  REQUIRE(services.connectivityService().tryPopAction(action));
  CHECK(action.type ==
        cadenza::system::ConnectivityActionType::ResetCredentials);
  REQUIRE(services.connectivityService().tryPopAction(action));
  CHECK(action.type ==
        cadenza::system::ConnectivityActionType::StartProvisioning);
}

TEST_CASE("Launcher settles Animation Gallery inside the decorated card") {
  for (const cadenza::FramebufferProfile profile : {
           cadenza::FramebufferProfile::TEmbed,
           cadenza::FramebufferProfile::Sharp}) {
    CAPTURE(static_cast<int>(profile));
    cadenza::LauncherApp launcher;
    NamedApp timer{"Timer"};
    NamedApp motion{"Motion"};
    NamedApp settings{"Settings"};
    NamedApp gallery{"Animation Gallery"};
    TextDiagnosticSink diagnostics;
    cadenza::AppRuntime runtime{profile, cadenza::kCutTransition};
    cadenza::system::SystemServiceHost services;
    runtime.setDiagnosticSink(&diagnostics);
    registerNamedApps(runtime, launcher, timer, motion, settings, gallery);
    cadenza::InputFrame selectGallery;
    selectGallery.turn = 3;
    cadenza::test::updateApp(launcher, 0.0F, selectGallery, runtime, services);
    for (int frame = 0; frame < 180 && !launcher.settled(); ++frame) {
      cadenza::test::updateApp(launcher, 1.0F / 60.0F, {}, runtime, services);
    }
    REQUIRE(launcher.settled());

    cadenza::MonoFramebuffer framebuffer{profile};
    cadenza::MonoCanvas canvas{framebuffer, &diagnostics};
    cadenza::test::renderApp(launcher, canvas, runtime, services);

    const int contentWidth = std::min(350, framebuffer.width() * 7 / 8);
    const int cardWidth = contentWidth + 6;
    const int cardHeight = contentWidth * 155 / 350 + 6;
    const int cardX = framebuffer.width() / 2 - cardWidth / 2;
    const int cardY = framebuffer.height() / 2 - cardHeight / 2;
    for (int y = cardY; y < cardY + cardHeight; ++y) {
      CHECK(framebuffer.pixel(cardX, y));
      CHECK(framebuffer.pixel(cardX + cardWidth - 1, y));
    }
    CHECK_FALSE(diagnostics.textClipped);
    CHECK_FALSE(diagnostics.invalidGeometry);
    CHECK_FALSE(diagnostics.unexpectedGeometryClip);
  }
}

TEST_CASE("Launcher card labels never invade the navigation slot") {
  for (const cadenza::FramebufferProfile profile : {
           cadenza::FramebufferProfile::TEmbed,
           cadenza::FramebufferProfile::Sharp}) {
    CAPTURE(static_cast<int>(profile));
    cadenza::LauncherApp shortLauncher;
    NamedApp shortClock{"A"};
    NamedApp shortMotion{"B"};
    NamedApp shortSettings{"C"};
    NamedApp shortGallery{"D"};
    cadenza::AppRuntime shortRuntime{profile, cadenza::kCutTransition};
    cadenza::system::SystemServiceHost shortServices;
    registerNamedApps(shortRuntime, shortLauncher, shortClock, shortMotion,
                      shortSettings, shortGallery);
    cadenza::MonoFramebuffer shortFrame{profile};
    cadenza::MonoCanvas shortCanvas{shortFrame};
    cadenza::test::renderApp(shortLauncher, shortCanvas, shortRuntime,
                             shortServices);

    cadenza::LauncherApp longLauncher;
    NamedApp longTimer{"TIMER WITH AN EXTREMELY LONG NAME"};
    NamedApp longMotion{"MOTION WITH AN EXTREMELY LONG NAME"};
    NamedApp longSettings{"SETTINGS WITH AN EXTREMELY LONG NAME"};
    NamedApp longGallery{"GALLERY WITH AN EXTREMELY LONG NAME"};
    TextDiagnosticSink diagnostics;
    cadenza::AppRuntime longRuntime{profile, cadenza::kCutTransition};
    cadenza::system::SystemServiceHost longServices;
    longRuntime.setDiagnosticSink(&diagnostics);
    registerNamedApps(longRuntime, longLauncher, longTimer, longMotion,
                      longSettings, longGallery);
    cadenza::MonoFramebuffer longFrame{profile};
    cadenza::MonoCanvas longCanvas{longFrame, &diagnostics};
    cadenza::test::renderApp(longLauncher, longCanvas, longRuntime,
                             longServices);

    const int centerX = shortFrame.width() / 2;
    const int footerY = shortFrame.height() - 17;
    for (int y = footerY - 5; y <= footerY + 5; ++y) {
      for (int x = centerX - 28; x <= centerX + 28; ++x) {
        CHECK(longFrame.pixel(x, y) == shortFrame.pixel(x, y));
      }
    }
    CHECK_FALSE(diagnostics.textClipped);
    CHECK_FALSE(diagnostics.invalidGeometry);
  }
}

TEST_CASE("Launcher directions expose neighbors and intermediate motion") {
  for (const cadenza::FramebufferProfile profile : {
           cadenza::FramebufferProfile::TEmbed,
           cadenza::FramebufferProfile::Sharp}) {
    CAPTURE(static_cast<int>(profile));
    cadenza::LauncherApp launcher;
    NamedApp timer{"TIMER WITH AN EXTREMELY LONG NAME"};
    NamedApp motion{"Motion"};
    NamedApp settings{"Settings"};
    NamedApp gallery{"Gallery"};
    cadenza::AppRuntime runtime{profile, cadenza::kCutTransition};
    cadenza::system::SystemServiceHost services;
    registerNamedApps(runtime, launcher, timer, motion, settings, gallery);
    TextDiagnosticSink diagnostics;
    cadenza::MonoFramebuffer framebuffer{profile};
    cadenza::MonoCanvas canvas{framebuffer, &diagnostics};

    cadenza::test::renderApp(launcher, canvas, runtime, services);
    const std::vector<std::uint8_t> vertical(
        framebuffer.data(), framebuffer.data() + framebuffer.sizeBytes());
    const int headerHeight = framebuffer.height() < 200 ? 22 : 27;
    CHECK(hasBlackInRect(framebuffer,
                         {0, headerHeight + 2, framebuffer.width(), 20}));
    CHECK(hasBlackInRect(framebuffer,
                         {0, framebuffer.height() - 20,
                          framebuffer.width(), 20}));

    cadenza::InputFrame turn;
    turn.turn = 1;
    cadenza::test::updateApp(launcher, 1.0F / 60.0F, turn, runtime, services);
    cadenza::test::renderApp(launcher, canvas, runtime, services);
    const std::vector<std::uint8_t> midpoint(
        framebuffer.data(), framebuffer.data() + framebuffer.sizeBytes());
    CHECK(midpoint != vertical);
    for (int frame = 0; frame < 180 && !launcher.settled(); ++frame) {
      cadenza::test::updateApp(launcher, 1.0F / 60.0F, {}, runtime, services);
    }
    cadenza::test::renderApp(launcher, canvas, runtime, services);
    const std::vector<std::uint8_t> settled(
        framebuffer.data(), framebuffer.data() + framebuffer.sizeBytes());
    CHECK(settled != midpoint);

    REQUIRE(services.submit(cadenza::SystemCommand::setLauncherOrientation(
        cadenza::LauncherOrientation::Horizontal)));
    services.commitCommands();
    cadenza::test::renderApp(launcher, canvas, runtime, services);
    const std::vector<std::uint8_t> horizontal(
        framebuffer.data(), framebuffer.data() + framebuffer.sizeBytes());
    CHECK(horizontal != settled);
    CHECK(hasBlackInRect(framebuffer,
                         {0, headerHeight + 2, 24,
                          framebuffer.height() - headerHeight - 2}));
    CHECK(hasBlackInRect(framebuffer,
                         {framebuffer.width() - 24, headerHeight + 2, 24,
                          framebuffer.height() - headerHeight - 2}));
    CHECK_FALSE(diagnostics.textClipped);
    CHECK_FALSE(diagnostics.invalidGeometry);
    CHECK_FALSE(diagnostics.unexpectedGeometryClip);
  }
}

TEST_CASE("settled Launcher framebuffer is independent of elapsed time") {
  cadenza::LauncherApp launcher;
  NamedApp timer{"Timer"};
  NamedApp motion{"Motion"};
  NamedApp settings{"Settings"};
  NamedApp gallery{"Gallery"};
  cadenza::AppRuntime runtime;
  cadenza::system::SystemServiceHost services;
  registerNamedApps(runtime, launcher, timer, motion, settings, gallery);
  for (int frame = 0; frame < 180 && !launcher.settled(); ++frame) {
    cadenza::test::updateApp(launcher, 1.0F / 60.0F, {}, runtime, services);
  }
  REQUIRE(launcher.settled());
  cadenza::MonoFramebuffer framebuffer{cadenza::FramebufferProfile::TEmbed};
  cadenza::MonoCanvas canvas{framebuffer};
  cadenza::test::renderApp(launcher, canvas, runtime, services);
  const std::vector<std::uint8_t> before(
      framebuffer.data(), framebuffer.data() + framebuffer.sizeBytes());
  cadenza::test::updateApp(launcher, 0.5F, {}, runtime, services);
  cadenza::test::renderApp(launcher, canvas, runtime, services);
  const std::vector<std::uint8_t> after(
      framebuffer.data(), framebuffer.data() + framebuffer.sizeBytes());
  CHECK(after == before);
}
