SuperTapir/CadenzaOS/tests/app_runtime_tests.cpp

#define DOCTEST_CONFIG_IMPLEMENT_WITH_MAIN
#include "doctest.h"

#include <array>
#include <cstdint>
#include <string>
#include <vector>

#include "cadenza/core/app_runtime.h"
#include "cadenza/core/app_catalog.h"
#include "cadenza/system/frame_coordinator.h"
#include "cadenza/system/system_service_host.h"

namespace {
constexpr cadenza::AppId kHomeAppId{1};
constexpr cadenza::AppId kTimerAppId{2};
constexpr cadenza::AppId kMotionAppId{3};
constexpr cadenza::AppId kMissingAppId{4};

std::uint64_t pcmHash(const std::int16_t* samples, std::size_t count) {
  std::uint64_t hash = 1469598103934665603ULL;
  for (std::size_t index = 0; index < count; ++index) {
    const auto value = static_cast<std::uint16_t>(samples[index]);
    hash = (hash ^ static_cast<std::uint8_t>(value & 0xFFU)) *
           1099511628211ULL;
    hash = (hash ^ static_cast<std::uint8_t>(value >> 8U)) *
           1099511628211ULL;
  }
  return hash;
}

std::uint64_t frameHash(const cadenza::MonoFramebuffer& framebuffer) {
  std::uint64_t hash = 1469598103934665603ULL;
  for (std::size_t index = 0; index < framebuffer.sizeBytes(); ++index) {
    hash = (hash ^ framebuffer.data()[index]) * 1099511628211ULL;
  }
  return hash;
}

class FakeApp final : public cadenza::App {
 public:
  FakeApp(const char* appName, std::vector<std::string>& events)
      : appName_(appName), events_(events) {}

  const char* name() const noexcept override { return appName_; }
  void onEnter() noexcept override { events_.push_back(std::string(appName_) + ":enter"); }
  void onExit() noexcept override { events_.push_back(std::string(appName_) + ":exit"); }
  void update(const cadenza::AppUpdateContext&) noexcept override {
    ++updates;
    events_.push_back(std::string(appName_) + ":update");
  }
  void render(cadenza::MonoCanvas&,
              const cadenza::AppRenderContext&) noexcept override {
    ++renders;
  }

  int updates = 0;
  int renders = 0;

 private:
  const char* appName_;
  std::vector<std::string>& events_;
};

struct Fixture {
  std::vector<std::string> events;
  FakeApp launcher{"Launcher", events};
  FakeApp timer{"Timer", events};
  FakeApp motion{"Motion", events};
  cadenza::AppRuntime runtime;
  cadenza::system::SystemServiceHost services;

  explicit Fixture(cadenza::FramebufferProfile profile =
                       cadenza::FramebufferProfile::TEmbed)
      : runtime{profile} {
    REQUIRE(runtime.registerApp(kHomeAppId, launcher, false));
    REQUIRE(runtime.registerApp(kTimerAppId, timer));
    REQUIRE(runtime.registerApp(kMotionAppId, motion));
    REQUIRE(runtime.configureHome(kHomeAppId));
    runtime.bindSystem(services.snapshot(), services);
  }

  void update(cadenza::Seconds dt,
              const cadenza::InputFrame& input = {}) noexcept {
    const auto& snapshot = services.beginFrame(dt);
    runtime.updateWithSystem(dt, input, snapshot, services);
    services.commitCommands();
  }
};
}  // namespace

TEST_CASE("runtime registry preserves static IDs visibility and names") {
  Fixture fixture;
  CHECK(fixture.runtime.launcherAppCount() == 2);
  CHECK(fixture.runtime.launcherAppAt(0) == kTimerAppId);
  CHECK(fixture.runtime.launcherAppAt(1) == kMotionAppId);
  CHECK(fixture.runtime.launcherAppAt(99) == kHomeAppId);
  CHECK(std::string(fixture.runtime.appName(kMotionAppId)) == "Motion");
  CHECK(std::string(fixture.runtime.appName(kMissingAppId)) == "MISSING");
  CHECK_FALSE(fixture.runtime.registerApp({}, fixture.timer));
}

TEST_CASE("AppId is a stable value type with an explicit invalid value") {
  constexpr cadenza::AppId unknownToCore{0x4321};
  static_assert(unknownToCore.valid());
  static_assert(unknownToCore.value() == 0x4321);
  static_assert(!cadenza::AppId{}.valid());

  std::vector<std::string> events;
  FakeApp app{"External", events};
  cadenza::AppRuntime runtime;
  REQUIRE(runtime.registerApp(unknownToCore, app));
  REQUIRE(runtime.begin(unknownToCore));
  runtime.update(0.01F, {});
  CHECK(app.updates == 1);
}

TEST_CASE("catalog rejects invalid duplicate and capacity without mutation") {
  std::vector<std::string> events;
  FakeApp first{"First", events};
  FakeApp second{"Second", events};
  FakeApp third{"Third", events};
  cadenza::AppCatalog catalog{2};

  cadenza::AppDescriptor missingApp;
  missingApp.id = cadenza::AppId{8};
  CHECK(catalog.registerApp(missingApp) ==
        cadenza::AppRegistrationResult::InvalidId);

  CHECK(catalog.registerApp({}, first, true) ==
        cadenza::AppRegistrationResult::InvalidId);
  CHECK(catalog.registerApp(
            cadenza::AppId{9}, first, true, "First",
            cadenza::AppCapabilitySet::fromRaw(0x80000000U)) ==
        cadenza::AppRegistrationResult::UnknownCapabilities);
  CHECK(catalog.registerApp(cadenza::AppId{10}, first, true) ==
        cadenza::AppRegistrationResult::Registered);
  CHECK(catalog.registerApp(cadenza::AppId{10}, second, false) ==
        cadenza::AppRegistrationResult::DuplicateId);
  CHECK(catalog.registerApp(cadenza::AppId{20}, second, false) ==
        cadenza::AppRegistrationResult::Registered);
  CHECK(catalog.registerApp(cadenza::AppId{30}, third, true) ==
        cadenza::AppRegistrationResult::CapacityExceeded);

  CHECK(catalog.size() == 2);
  CHECK(catalog.at(0)->id == cadenza::AppId{10});
  CHECK(catalog.at(0)->app == &first);
  CHECK(catalog.at(0)->visibleInLauncher);
  CHECK(catalog.at(0)->capabilities.empty());
  CHECK(catalog.at(1)->id == cadenza::AppId{20});
  CHECK(catalog.at(1)->app == &second);
  CHECK_FALSE(catalog.at(1)->visibleInLauncher);
}

TEST_CASE("system menu Home uses the composition root configured Home App") {
  std::vector<std::string> events;
  FakeApp home{"CustomHome", events};
  FakeApp child{"Child", events};
  cadenza::AppRuntime runtime;
  REQUIRE(runtime.registerApp(cadenza::AppId{77}, home, false));
  REQUIRE(runtime.registerApp(cadenza::AppId{88}, child));
  REQUIRE(runtime.configureHome(cadenza::AppId{77}));
  REQUIRE(runtime.begin(cadenza::AppId{88}));

  cadenza::InputFrame input;
  input.longPressed = true;
  runtime.update(0.01F, input);
  REQUIRE(runtime.systemMenuActive());
  CHECK_FALSE(runtime.transitioning());
  cadenza::InputFrame release;
  release.released = true;
  runtime.update(0.01F, release);
  cadenza::InputFrame turn;
  turn.turn = 1;
  runtime.update(0.01F, turn);
  cadenza::InputFrame click;
  click.clicked = true;
  click.released = true;
  runtime.update(0.01F, click);
  REQUIRE(runtime.transitioning());
  runtime.update(0.33F, {});
  CHECK(runtime.currentId() == cadenza::AppId{77});
  CHECK(events == std::vector<std::string>{"Child:enter", "Child:exit",
                                           "CustomHome:enter"});
}

TEST_CASE("begin enters one valid initial App exactly once") {
  Fixture fixture;
  CHECK_FALSE(fixture.runtime.begin(kMissingAppId));
  CHECK(fixture.events.empty());
  REQUIRE(fixture.runtime.begin(kHomeAppId));
  CHECK(fixture.events == std::vector<std::string>{"Launcher:enter"});
  CHECK_FALSE(fixture.runtime.begin(kTimerAppId));
  CHECK(fixture.runtime.currentId() == kHomeAppId);
}

TEST_CASE("open guards current missing invalid and in-flight destinations") {
  Fixture fixture;
  REQUIRE(fixture.runtime.begin(kHomeAppId));
  CHECK_FALSE(fixture.runtime.open(kHomeAppId));
  CHECK_FALSE(fixture.runtime.open(kMissingAppId));
  CHECK_FALSE(fixture.runtime.open({}));
  REQUIRE(fixture.runtime.open(kTimerAppId));
  CHECK(fixture.runtime.transitioning());
  CHECK(fixture.services.pendingCommandCount() == 1);
  CHECK_FALSE(fixture.runtime.open(kMotionAppId));
  CHECK(fixture.services.pendingCommandCount() == 1);
}

TEST_CASE("transition orders exit before enter at the midpoint") {
  Fixture fixture;
  REQUIRE(fixture.runtime.begin(kHomeAppId));
  REQUIRE(fixture.runtime.open(kTimerAppId));
  fixture.update(0.39F);
  CHECK(fixture.events == std::vector<std::string>{"Launcher:enter"});
  fixture.update(0.02F);
  CHECK(fixture.events ==
        std::vector<std::string>{"Launcher:enter", "Launcher:exit", "Timer:enter"});
  CHECK(fixture.runtime.currentId() == kTimerAppId);
}

TEST_CASE("only active App updates and transition input is frozen") {
  Fixture fixture;
  REQUIRE(fixture.runtime.begin(kHomeAppId));
  cadenza::InputFrame input;
  input.turn = 3;
  input.clicked = true;
  fixture.update(0.01F, input);
  CHECK(fixture.launcher.updates == 1);
  REQUIRE(fixture.runtime.open(kTimerAppId));
  input.turn = 7;
  fixture.update(0.10F, input);
  fixture.update(0.71F, input);
  CHECK_FALSE(fixture.runtime.transitioning());
  CHECK(fixture.launcher.updates == 1);
  CHECK(fixture.timer.updates == 0);
  fixture.update(0.01F);
  CHECK(fixture.timer.updates == 1);
}

TEST_CASE("long press opens system menu without updating active App") {
  Fixture fixture;
  REQUIRE(fixture.runtime.begin(kTimerAppId));
  cadenza::InputFrame input;
  input.longPressed = true;
  fixture.update(0.01F, input);
  CHECK(fixture.runtime.systemMenuActive());
  CHECK_FALSE(fixture.runtime.transitioning());
  CHECK(fixture.runtime.currentId() == kTimerAppId);
  CHECK(fixture.timer.updates == 0);
  CHECK(fixture.services.sound().lastAcceptedCue() ==
        cadenza::audio::SoundCue::MenuOpen);
  CHECK(fixture.services.sound().pendingCommandCount() == 1);
  fixture.update(0.17F);
  CHECK(fixture.runtime.currentId() == kTimerAppId);
  CHECK(fixture.events == std::vector<std::string>{"Timer:enter"});
}

TEST_CASE("App actions and system menu surfaces use distinct semantic cues") {
  constexpr std::size_t kSamples = 44100;
  Fixture fixture;
  REQUIRE(fixture.runtime.begin(kHomeAppId));

  REQUIRE(fixture.runtime.open(kTimerAppId));
  fixture.update(0.01F);
  CHECK(fixture.services.sound().lastAcceptedCue() ==
        cadenza::audio::SoundCue::Confirm);
  std::array<std::int16_t, kSamples> pcm{};
  fixture.services.renderAudio(pcm.data(), pcm.size());
  CHECK(pcmHash(pcm.data(), pcm.size()) == 0x718BD5DCD3F36003ULL);

  fixture.update(0.79F);
  REQUIRE(fixture.runtime.currentId() == kTimerAppId);
  cadenza::InputFrame input;
  input.longPressed = true;
  fixture.update(0.01F, input);
  CHECK(fixture.services.sound().lastAcceptedCue() ==
        cadenza::audio::SoundCue::MenuOpen);
  pcm.fill(0);
  fixture.services.renderAudio(pcm.data(), pcm.size());
  CHECK(pcmHash(pcm.data(), pcm.size()) == 0xFFD867CDEBDCD06AULL);

  cadenza::InputFrame released;
  released.released = true;
  fixture.update(0.01F, released);
  fixture.update(0.01F, input);
  CHECK(fixture.runtime.systemMenuActive());
  CHECK(fixture.runtime.systemSurfaces().menuClosing());
  CHECK(fixture.services.sound().lastAcceptedCue() ==
        cadenza::audio::SoundCue::MenuClose);
  pcm.fill(0);
  fixture.services.renderAudio(pcm.data(), pcm.size());
  CHECK(pcmHash(pcm.data(), pcm.size()) == 0xBC8674B8C5CA39A5ULL);
  CHECK(fixture.runtime.systemSurfaces().diagnostics().closed == 1);
  const auto pendingAfterClose =
      fixture.services.sound().pendingCommandCount();
  fixture.update(0.17F);
  CHECK_FALSE(fixture.runtime.systemMenuActive());
  CHECK(fixture.runtime.systemSurfaces().diagnostics().closed == 1);
  CHECK(fixture.services.sound().pendingCommandCount() == pendingAfterClose);
}

TEST_CASE("system menu freezes App lifecycle while services keep advancing") {
  Fixture fixture;
  REQUIRE(fixture.runtime.begin(kTimerAppId));
  cadenza::MonoFramebuffer framebuffer{cadenza::FramebufferProfile::TEmbed};
  cadenza::MonoCanvas canvas{framebuffer};

  cadenza::system::FrameCoordinator::runFrame(
      fixture.services, fixture.runtime, canvas, 0.01F, {});
  const int updatesBeforeMenu = fixture.timer.updates;
  const int rendersBeforeMenu = fixture.timer.renders;
  cadenza::InputFrame input;
  input.longPressed = true;
  cadenza::system::FrameCoordinator::runFrame(
      fixture.services, fixture.runtime, canvas, 0.01F, input);
  const int frozenRenderCount = fixture.timer.renders;
  CHECK(frozenRenderCount == rendersBeforeMenu);
  REQUIRE(fixture.services.postPlatformEvent(
      cadenza::system::PlatformEvent::soundOutputAvailability(true)));
  cadenza::InputFrame release;
  release.released = true;
  cadenza::system::FrameCoordinator::runFrame(
      fixture.services, fixture.runtime, canvas, 0.05F, release);
  cadenza::system::FrameCoordinator::runFrame(
      fixture.services, fixture.runtime, canvas, 0.05F, {});

  CHECK(fixture.timer.updates == updatesBeforeMenu);
  CHECK(fixture.timer.renders == frozenRenderCount);
  CHECK(fixture.services.snapshot().soundOutputAvailable);
  CHECK(fixture.events == std::vector<std::string>{"Timer:enter", "Timer:update"});
}

TEST_CASE("menu request during transition opens on stable destination") {
  Fixture fixture;
  REQUIRE(fixture.runtime.begin(kHomeAppId));
  REQUIRE(fixture.runtime.open(kTimerAppId));
  cadenza::InputFrame held;
  held.longPressed = true;
  fixture.update(0.10F, held);
  CHECK(fixture.runtime.systemSurfaces().hasDeferredMenu());
  CHECK_FALSE(fixture.runtime.systemMenuActive());
  cadenza::InputFrame release;
  release.released = true;
  fixture.update(0.71F, release);
  CHECK_FALSE(fixture.runtime.transitioning());
  CHECK(fixture.runtime.currentId() == kTimerAppId);
  CHECK_FALSE(fixture.runtime.systemMenuActive());
  fixture.update(0.01F);
  CHECK(fixture.runtime.systemMenuActive());
  CHECK(fixture.timer.updates == 0);
}

TEST_CASE("system menu setting action commits through typed system command") {
  Fixture fixture;
  REQUIRE(fixture.runtime.begin(kTimerAppId));
  cadenza::MonoFramebuffer framebuffer{cadenza::FramebufferProfile::TEmbed};
  cadenza::MonoCanvas canvas{framebuffer};
  cadenza::InputFrame held;
  held.longPressed = true;
  cadenza::system::FrameCoordinator::runFrame(
      fixture.services, fixture.runtime, canvas, 0.01F, held);
  cadenza::InputFrame release;
  release.released = true;
  cadenza::system::FrameCoordinator::runFrame(
      fixture.services, fixture.runtime, canvas, 0.01F, release);
  cadenza::InputFrame selectSound;
  selectSound.turn = 2;
  cadenza::system::FrameCoordinator::runFrame(
      fixture.services, fixture.runtime, canvas, 0.01F, selectSound);
  REQUIRE(fixture.runtime.systemMenuSelection() ==
          cadenza::presentation::SystemMenuItem::Sound);
  cadenza::InputFrame click;
  click.clicked = true;
  click.released = true;
  cadenza::system::FrameCoordinator::runFrame(
      fixture.services, fixture.runtime, canvas, 0.01F, click);
  CHECK(fixture.services.snapshot().soundVolume ==
        cadenza::audio::SoundVolume::High);
  CHECK(fixture.runtime.systemMenuActive());
}

TEST_CASE("background Timer indicator is HomeOnly") {
  Fixture fixture;
  REQUIRE(fixture.runtime.begin(kHomeAppId));
  cadenza::MonoFramebuffer framebuffer{cadenza::FramebufferProfile::TEmbed};
  cadenza::MonoCanvas canvas{framebuffer};

  cadenza::SystemSnapshot snapshot;
  fixture.runtime.renderWithSystem(canvas, snapshot);
  const std::uint64_t homeBaseline = frameHash(framebuffer);

  snapshot.timer.state = cadenza::TimerState::Running;
  snapshot.timer.owner = kTimerAppId;
  snapshot.timer.remainingMs = 7 * 60000 + 18000;
  fixture.runtime.renderWithSystem(canvas, snapshot);
  const std::uint64_t homeRunning = frameHash(framebuffer);
  CHECK(homeRunning != homeBaseline);
  CHECK_FALSE(framebuffer.pixel(2, 2));
  CHECK_FALSE(framebuffer.pixel(31, 3));
  CHECK(framebuffer.pixel(31, 4));

  snapshot.timer.state = cadenza::TimerState::Paused;
  fixture.runtime.renderWithSystem(canvas, snapshot);
  CHECK(frameHash(framebuffer) != homeRunning);

  REQUIRE(fixture.runtime.open(kMotionAppId));
  while (fixture.runtime.transitioning()) {
    fixture.update(1.0F / 60.0F);
  }
  snapshot.timer.state = cadenza::TimerState::Ready;
  framebuffer.clear(false);
  fixture.runtime.renderWithSystem(canvas, snapshot);
  const std::uint64_t motionReady = frameHash(framebuffer);
  snapshot.timer.state = cadenza::TimerState::Running;
  framebuffer.clear(false);
  fixture.runtime.renderWithSystem(canvas, snapshot);
  CHECK(frameHash(framebuffer) == motionReady);
  CHECK_FALSE(framebuffer.pixel(31, 4));
}

TEST_CASE("passive indicators retract on leave Home and pop on return") {
  Fixture fixture;
  REQUIRE(fixture.runtime.begin(kHomeAppId));
  cadenza::MonoFramebuffer framebuffer{cadenza::FramebufferProfile::TEmbed};
  cadenza::MonoCanvas canvas{framebuffer};
  cadenza::SystemSnapshot snapshot;
  snapshot.timer.state = cadenza::TimerState::Running;
  snapshot.timer.owner = kTimerAppId;
  snapshot.timer.remainingMs = 8 * 60000;
  fixture.runtime.bindSystem(snapshot, fixture.services);
  CHECK(fixture.runtime.passiveIndicatorSlide() == doctest::Approx(1.0F));

  REQUIRE(fixture.runtime.open(kMotionAppId));
  float previous = fixture.runtime.passiveIndicatorSlide();
  bool sawDecrease = false;
  while (fixture.runtime.transitioning()) {
    fixture.services.beginFrame(1.0F / 60.0F);
    fixture.runtime.updateWithSystem(1.0F / 60.0F, {},
                                     fixture.services.snapshot(),
                                     fixture.services);
    fixture.services.commitCommands();
    const float slide = fixture.runtime.passiveIndicatorSlide();
    if (slide < previous) sawDecrease = true;
    previous = slide;
  }
  CHECK(sawDecrease);
  CHECK(fixture.runtime.passiveIndicatorSlide() == doctest::Approx(0.0F));
  fixture.runtime.renderWithSystem(canvas, snapshot);
  CHECK_FALSE(framebuffer.pixel(31, 4));

  REQUIRE(fixture.runtime.open(kHomeAppId));
  bool sawIncrease = false;
  previous = fixture.runtime.passiveIndicatorSlide();
  while (fixture.runtime.transitioning()) {
    cadenza::SystemSnapshot returning = fixture.services.beginFrame(1.0F / 60.0F);
    returning.timer = snapshot.timer;
    fixture.runtime.updateWithSystem(1.0F / 60.0F, {}, returning,
                                     fixture.services);
    fixture.services.commitCommands();
    const float slide = fixture.runtime.passiveIndicatorSlide();
    if (slide > previous) sawIncrease = true;
    previous = slide;
  }
  CHECK(sawIncrease);
  CHECK(fixture.runtime.passiveIndicatorSlide() == doctest::Approx(1.0F));
  framebuffer.clear(false);
  fixture.runtime.renderWithSystem(canvas, snapshot);
  CHECK(framebuffer.pixel(31, 4));
}

TEST_CASE("background Timer indicator contains 99-minute label on Home") {
  for (const auto profile : {cadenza::FramebufferProfile::TEmbed,
                             cadenza::FramebufferProfile::Sharp}) {
    CAPTURE(static_cast<int>(profile));
    Fixture fixture{profile};
    REQUIRE(fixture.runtime.begin(kHomeAppId));
    cadenza::MonoFramebuffer framebuffer{profile};
    cadenza::MonoCanvas canvas{framebuffer};

    cadenza::SystemSnapshot snapshot;
    snapshot.timer.owner = kTimerAppId;
    snapshot.timer.remainingMs = 99 * 60000;
    for (const auto state : {cadenza::TimerState::Running,
                             cadenza::TimerState::Paused}) {
      CAPTURE(static_cast<int>(state));
      framebuffer.clear(false);
      snapshot.timer.state = state;
      fixture.runtime.renderWithSystem(canvas, snapshot);

      const char* label = state == cadenza::TimerState::Running ? "T 99"
                                                                : "P 99";
      const auto metrics =
          canvas.measureText(label, cadenza::TextRole::Compact);
      constexpr int kLabelLeft = 14;
      const int rightPadding = kLabelLeft + metrics.width;
      CHECK(framebuffer.pixel(rightPadding, 16));
    }
  }
}
